eduarbo/flan36/docs/progress.md

# Progress

**Current mechanical revision: I. Overall keyboard: partial digital prototype.**

| Outcome | State | Evidence / next step |
|---|---|---|
| 36 Piantor key centers and angles | Checked | [Layout](../design/layout.json), upstream files and checker |
| Editable source and CAD exchange | Available | Native FCStd, parameters and [FreeCAD/StepUp examples](freecad.md) |
| KLP catalog and themed frames | RevI digital study | 38 source variants, 28 with qualified positions; six installed approved frame styles, per-key colors and configuration export/import |
| Wireless electronics and displays | Routed prototype | Both halves: DRC/ERC/parity 0, unconnected 0; exact connectors and hardware tests pending |
| Firmware and fabrication files | Digital candidate | Three compiled UF2 variants and source-bound Gerber/drill packages; supplied parts and physical acceptance pending |
| Printing and assembly | Pending | Fit coupon, sample caps and actual component measurements |
| Working keyboard | Pending | All keys, BLE, charging, sleep/wake and measured consumption |

## Revision I — October audit corrections

The current assembly adds the approved Hanafuda frame, repairs display/frame parameter dependencies and case USB access, and includes all 36 diodes and hot-swap sockets. Current delivery evidence and remaining prototype limits are recorded in the [audit correction report](reviews/2026-10-07-corrections.md).

Publication verified: **1,875 source files**, the online/offline viewer, print resources and thirteen rendered images match the tested source. The public viewer preserves the camera through case/frame changes and exports the selected configuration and exact STL kit. [Publication evidence](../validation/revI-audit-publication.json). This is a historical publication snapshot. Current routing and firmware evidence is in the [build continuation](reviews/2026-10-08-build-continuation.md); physical acceptance remains open.

The entries below retain their original historical snapshots.

## Revision I — readable right-hand artwork

Both halves now keep the same artwork direction. Game Boy's D-pad stays on the left and its buttons on the right; the right shell retains its existing corner radii and mounting geometry. The correction is recorded in the native document and carried through the material STL/STEP files, viewer and print kit. Historical documents retain their original interpretation. [Construction and checks](../design/frame-orientation.md).

## Revision I — approved viewer selection

The earlier withdrawal changed only the proposal gallery, leaving rejected shapes in the main viewer. The viewer now offers Talavera (default), Game Boy, SNES, Phone and iPod; Flan, Tape, Orbit, Manga, NES and Walkman are excluded from its selector, geometry and print kit. Saved and imported retired IDs migrate to Talavera with original colors and recoverable source JSON. Hanafuda remains approved but not integrated. [Correction and reproducible checks](../design/approved-viewer-selection.md).

## Revision I — approved gallery selection (earlier snapshot)

The user rejected Evangelion and requested its removal. The [current gallery](frame-proposals.md) now contains only Talavera, Game Boy, SNES, Phone, iPod and Hanafuda. The rejected proposal and its public previews were removed from the gallery. There is no pending artwork approval. Hanafuda integration remains pending; the main assembly and explorer are unchanged. [Selection record](../design/frame-selection.json).

## Revision I — historical R8 proposal

[R8](../design/proposals/frame-redesign-r8/) retained the six approved designs and proposed an Evangelion frame using M1's palette. That proposal was subsequently rejected and never installed. Historical source and verification receipts are preserved.

## Revision I — Hanafuda retained; historical R7 choices

The user selected Hanafuda with its R6 shapes and palette unchanged. Caramelo, Lucha, Cartucho 8 and Terminal were rejected; the previous Mecha was rejected for redesign. [R7](../design/proposals/frame-redesign-r7/) offered three Mecha and three Kumiko alternatives with exact dimensions, colors and matching review solids. Selection precedes artwork integration; the production assembly and main viewer are unchanged.

## Revision I — six new artwork directions, historical R6

R5 was rejected. [R6](../design/proposals/frame-redesign-r6/) proposed Caramelo, Lucha, Hanafuda, Mecha, Cartucho 8 and Terminal with exact paths, solid HEX colors, dimensioned sheets and matching editable FreeCAD review solids. Subsequent selection is recorded above; the frozen proposal files remain available.

## Revision I — corrected display seam and six exact proposals

The opening is now centered on the glass with 0.10 mm nominal clearance on all sides. It closes the exposed side bands without moving the display or raising the stack. The five approved bezels remain exactly 2.40 mm wide; their other artwork and colors are unchanged. [Correction and limits](../design/display-seam-implementation.md).

Flan, Tape, Orbit, Manga, NES and Walkman received [dimensioned R5 proposals](../design/proposals/frame-redesign-r5/), including editable review solids and actual mesh renders. This historical proposal was subsequently rejected and superseded by R6; its artwork was never installed. [Verified public source, viewer, print kit and R5 snapshot](../validation/revI-display-seam-public.json).

## Revision I — approved R4 frames (earlier snapshot)

Talavera, Game Boy, SNES, 2000s Phone and iPod now use the approved exact paths and solid palettes. The frame and Level shell rise 0.20 mm to Z13.59; the centered glass stays at Z13.39 and the pin row gains a 0.40 mm cover. Flan, Tape, Orbit, Manga, NES and Walkman retain their existing artwork pending redesign. Flan remains the default. [Construction and verification](frames-extra.md). Public source, viewer, images and an actual print-kit download match the implemented files. [Public readback](../validation/revI-approved-frames-public.json).

The entries below describe their historical snapshots. Their receipts retain original hashes.

## Revision I — frame fidelity correction

The first collection passed structural checks but did not preserve the selected compositions, and its support mask silently severed several decorations. The correction restores the reference motifs and adds per-feature rejection for unsupported artwork. [Reference comparison](frame-comparison.md) · [Digital checks](../validation/revI-frame-fidelity.json). Earlier verification receipts describe their original snapshots. Public source, images, viewer and downloaded print files match the corrected implementation. [Publication receipt](../validation/revI-frame-fidelity-public.json).

## Revision I — solid-color frame collection

Flan is the default frame in the native assembly, viewer and presets. Tape, Orbit, Manga, Talavera, Game Boy, NES, SNES, 2000s Phone, Walkman and iPod complete the new collection. Every design uses up to four solid colors in flush 0.4 mm co-print regions. The case, keys, electronics and 13.39 mm roof remain unchanged.

Older frame IDs migrate to Flan with the original saved bytes retained for recovery. Their colors, battery, cases and caps survive. The current exports contain only the eleven designs. [Collection and regeneration](frames-extra.md) · [Current digital checks](../validation/revI-frame-collection.json).

## Revision I — sculpted cap direction correction

The Normal and Saddle sculpted presets had the top and bottom rotations reversed. Both now place the higher edges away from the home row. This changes 20 rotations per preset, with no changes to stems, seating or key centers. Actual side-profile previews replace the former side-by-side arrangement. **Caps → Fix top/bottom slopes** repairs older configurations without replacing custom variants, colors or other components. [Directional checks](../validation/revI-cap-rows.json).

## Revision I — floor battery and Level case

The glass, frame and new **Level** upper shell share a **13.39 mm** plane: **1.41 mm lower** than the previous frame. Both batteries sit directly on the 1.4 mm case floor. The nice!nano PCB is at 8.2 mm and the nice!view PCB at 11.49 mm. Key centers and the selected caps' 17.87 mm height are unchanged.

Level covers switch bodies using the existing removable plate and its three screws. Its openings reserve the full 3.5 mm cap travel. The current collection has eleven flush frames, both battery profiles and twenty-seven linked color themes. [Dimensions and connector qualification](level-stack.md) · [Current digital delivery checks](../validation/revI-level-delivery.json).

The Samtec display pair is dimensioned as a nominal candidate. Finished nice!view hole fit, actual engagement, printed strength and physical assembly remain unqualified. The boards remain unrouted.

The entries below describe their historical snapshots. Current files may supersede their geometry; original receipts retain the hashes of the files tested at the time.

## Earlier revision I — slimmer stack and flush decoration

The electronics cover now targets **14.8 mm** from the case underside, with a **12.4 mm display PCB datum**. The battery moves 0.8 mm toward USB without rotation. A lateral PH connector, retained display socket and recessed underside reset make the interfaces explicit. Both Adafruit 1570 and 301230 have their own continuous nominal lead routes.

Handheld, Retro TV, Cyberpunk, Cartridge, Arcade, Mecha and Kintsugi use **0.4 mm flush color volumes** with at least 0.8 mm nominal backing. The ten frame styles, 36 original key transforms, case contour and magnetic interface are preserved. Selected KLP caps still set the overall 17.87 mm height, excluding feet.

[Design and service sequence](slim-flush.md) · [Historical digital delivery checks](../validation/revI-slim-flush.json). Exact supplied parts, wire flex, printed fits and electrical operation remain unqualified.

## Earlier revision I — keycap palettes and creative frames

Color all keys, a row, a column or one key, on either half or both. Eight keycap palettes and sixteen coordinated global themes provide starting points. Personal palettes can be saved, imported and exported; configurations retain all 36 colors without changing key shapes or rotations. [Color editor](customize.md#keycap-colors).

Cartridge, Arcade, Mecha and Kintsugi bring the frame catalog to ten. Their relief is actual printable geometry; previews and print kits use the corresponding meshes. Native FreeCAD preserves custom colors through save/reopen. [Frame guide](frames-extra.md).

The [measured support study](slim-mount-study.md) covers both halves, both batteries and all ten frames. Integrating plate washers removes six loose parts; optional integrated battery saddles remove two more. Neither changes height. A 15.6 mm plain roof clears modeled static geometry, but overall height stays **17.87 mm** with the selected caps, excluding feet. A 14.8 mm roof intersects the JST envelope. Display/sled extraction crosses modeled battery leads in all three recipes; cable routing, connector engagement and physical fit remain open. Separately named experimental STEP/STL files are included; the reference print kit keeps its original stack.

Publication verified: all **1,013 implementation files** match the anonymous archive. The public viewer passes desktop/touch checks, per-key palettes, coordinated themes, configuration/GLB round trips and six selected print kits. [Public readback](../validation/revI-customization-publication.json). Physical keyboard acceptance remains open.

## Earlier revision I — shared frame corner and height study

The USB-side frame corner now uses the case's actual R2.4 arc. The previous R1.2 frame produced a roughly 0.497 mm diagonal overhang. The cavity, plate clearance and beveled profiles follow that shared definition. Case/PCB outlines and key positions are unchanged. [Close view and height comparison](design.md#can-the-stack-be-thinner) · [Native corner check](../validation/revI-frame-corner.json).

That snapshot’s 16.6 mm plain / 17.2 mm decorated cover was **not a proven minimum**. A preliminary left-half study lowers the display and evaluates 15.6 / 16.2 mm covers; actual connector engagement and tolerances remain open. A 14.8 mm plain cover intersects the existing battery-connector envelope. Printable source heights remain unchanged. [Study](../validation/revI-stack-study.json) · [Correction scope](../design/corner-stack-workflow.json) · [Independent review](../validation/revI-corner-stack-review.json).

Publication verified: all **922 implementation files** matched the anonymous archive; public Pages, the corner image, desktop/touch UI and selected print exports matched the tested source. [Public readback](../validation/revI-corner-stack-publication.json).

## Revision I — linked colors, print kits and component models

Sixteen color themes coordinate the frame with the case rim. Per-half body, plate and three detail colors survive JSON and local browser storage; applying a theme preserves the selected shapes and keycaps. Print kits include the selected native STL parts, generic color 3MF files, supports, washers and the actual screw/magnet instructions. No clip variant is claimed. [Themes and printing](themes-printing.md).

The nice!nano v2 and nice!view now have nominal board/contact/package geometry. Choc v1 uses licensed KiSwitch meshes; the power and reset switches use KiCad models placed at the existing footprints. The narrower nano board uses scalloped support ledges, leaving the underside pad reserves clear. [Component evidence and limitations](../components/README.md).

The offline explorer passed desktop/touch emulation down to 320 px, per-half configuration and custom-color GLB export. Native FreeCAD preserved colors through save/reopen. Selected print kits preserve native STL bytes and closed, oriented 3MF surfaces. [Configuration checks](../validation/revI-theme-customization.json) · [Print checks](../validation/revI-print-kit.json).

With 4× CPU throttling, orbit p95 is **16.7 ms**, frame choice **68 ms** and case choice **124 ms**, with no orbit long tasks. First readiness takes **8.7 s** in this local stress test; the self-contained viewer is about **45 MiB**. Physical-phone loading and timing remain unmeasured. [Measurement](../validation/revI-theme-performance.json).

Publication verified: all **914 implementation files** matched the anonymous source archive. The actual public viewer passed desktop/touch emulation, 16 theme previews, linked colors, JSON/GLB and selected print-kit checks. All 11 relative KiCad STEP models passed geometry, footprint-placement and colored-surface readback. [Public verification](../validation/revI-themes-components-publication.json).

**Still partial:** Bambu Studio needs manual palette mapping; GUI import/save/reopen has not been validated. Hotswap socket registration, actual connector contacts, the 7 versus 8.8 mm display connection and physical fit remain open. [Scope and review](../design/themes-components-workflow.json).

## Revision I — local curves and interchangeable cases

The contour now follows each thumb’s angle with local tangent rounds, plus softer finger corners. Solid, Color rim and Terrace are real base/plate variants. Per-half choices and optional exposed display stacks transfer between the explorer, JSON, GLB and native FreeCAD. [Case gallery and files](cases.md) · [Decision record](../validation/revI-case-variants-review.json).

Native solids, all six case pairs, mixed configuration save/reopen and exact selected GLB meshes passed. The explorer uses distinct mesh previews in a two-column grid; desktop and touch emulation pass through 320 px. Local 4× CPU checks: orbit p95 **16.8 ms**, case selection p95 **123.5 ms**, frame selection p95 **68.6 ms**, zero orbit long tasks. Publication verified: **824 source files** match the anonymous archive; public viewer, case gallery images, desktop/touch interactions, per-half case selection, open covers and exact JSON/GLB exports pass. [Public readback](../validation/revI-case-variants-publication.json). Physical-phone timing and printed fit remain untested.

## Previous revision I — uniform exposed rim

That revision made the case, switch plate and PCB follow a **curved lower thumb edge and LCD-aligned flank**. The 2.55 mm thumb-side protrusion is removed without moving keys or widening the bay. Finger margins stay 4.75 mm; the pinky foot retains 90° backbone corners with R0.8 blends. View tools remain below the model, with clearer Part links/Fit view feedback and full-row explorer hover. [Measured view](images/revI-rim.png) · [Correction review](revI-review.md#key-aligned-local-curves-and-case-variants).

Publication verified: **785 source files** match the anonymous download. The public viewer passes desktop/touch emulation, layers, frame/battery selection, JSON and exact GLB checks; the dimensioned image matches its source. [Public readback](../validation/revI-rim-publication.json).

That revision’s local viewer check: 4× CPU orbit p95 **16.7 ms**, theme change p95 **64.6 ms**, and zero orbit long tasks. Desktop/touch emulation, layers, JSON and exact GLB exports pass. Physical-phone timing remains unmeasured.

## Earlier revision I — Contour, magnetic frames and dual battery cradle

The case and PCB follow the stepped reference: rectangular pinky foot, shallow recess and continuous thumb fan. The **117 × 92.85 mm** case uses 20 control corners at R0.8. All 36 original key transforms remain fixed.

Three captive magnet/steel stations release each frame vertically; five independent internal M2 screws retain the structure without adding perimeter lobes. Both nominal **Adafruit 1570 and 301230** envelopes share one low saddle, aperture and captured cage. The viewer and FreeCAD configuration include battery selection.

The viewer passed offline desktop and emulated mobile checks, exact selected battery/frame GLB exports and JSON round trips. Local 4× CPU measurements: **16.8 ms orbit p95**, **67 ms frame-change p95**, zero orbit long tasks. Physical-phone performance remains untested.

The earlier slot/copper conflict and displaced mount were corrected without relaxing the 0.5 mm edge rule. Native solids, six frame styles, two battery envelopes, saved configurations, CAD-derived renders and the viewer are checked as digital artifacts. Routing, connector qualification, printed retention, charging and BLE remain open.

Publication verified: all **775 source files** matched the anonymous archive; public viewer bytes and actual browser-loaded geometry matched the tested source. Desktop/touch emulation, batteries, frames, JSON and exact selected GLB geometry passed. [Public readback](../validation/revI-publication.json).

[Review and limits](revI-review.md) · [Mechanical checks](../validation/revI-mechanical.json) · [PCB readback](../validation/revI-electrical.json) · [Service/coupons](../validation/revI-service.json).

## Multicolor frame previews

Handheld, Retro TV and Cyberpunk now use distinct body, detail and accent colors on the existing raised faces. Larger upright previews show the corresponding meshes and palettes; one click applies both. Body-color overrides remain independent per half and survive JSON export/import. The shared palette also drives the GLB materials, FreeCAD configuration import and frame comparison image.

The former thumbnails referenced different STL files, but used one green material and a distant oblique view. Their distinct-image test did not establish readable design details. Current checks identify actual left/right raised features, preserve every original vertex/normal/triangle and verify the exported material colors. Geometry and manufacturing status remain unchanged.

Verified on the public viewer, including mobile emulation, JSON and GLB; all 579 published source files matched the tested commit. FreeCAD applied four colors per native theme/half and preserved them through save/reopen. The 4× CPU benchmark retained a 16.7 ms orbit p95 and 57.5 ms theme-change p95.

[Color and print guide](customize.md#print-a-themed-display-frame) · [Checks](../validation/viewer-multicolor.json) · [Public readback](../validation/viewer-multicolor-publication.json) · [Correction scope](../design/viewer-multicolor-workflow.json).

## Persistent component sidebar

All 12 component entries remain visible while their details scroll or collapse. Hover, focus or select a part to highlight it; the connecting line ends at its own sidebar entry. Frame previews still apply in one click. Desktop, 390 px and 320 px touch layouts, short landscape, configuration and exact GLB export passed local and public checks.

The previous floating-tag iteration passed functional tests but missed the intended sidebar relationship and had no latency acceptance. Its anchor search could run up to 192 full-scene intersection queries per camera update. Surface searching now pauses during gestures and resolves only the active component afterward; rendering is coalesced and highlights are reused.

On the same Chromium 152 setup at 1200 × 800 with 4× CPU throttling, **p95 orbit frame interval fell from 1,616.5 to 16.8 ms**, with 59 long tasks reduced to zero. **Frame-change p95 fell from 1,692.4 to 59.0 ms**. These are local benchmark results; physical-phone performance remains untested.

[Usage guide](viewer.md) · [Checks and measurements](../validation/viewer-sidebar.json) · [Public readback](../validation/viewer-sidebar-publication.json), including all 571 source-commit files · [Correction scope](../design/viewer-sidebar-workflow.json). Historical acceptance of the first visual explorer remains in its [original receipt](../validation/viewer-ux-publication.json).

## Revision H — continuous edge and printable themes

The user’s red-line reference replaces the old display notch and thumb wing with one straight inner case flank. The case is approximately **8.1 mm narrower**, keeping every switch center and angle. Sixteen intentional corners use a common **1.2 mm radius**.

Handheld, Retro TV and Cyberpunk add actual roof relief within the same bay. Plain styles remain available. The high cover ends before the thumb; base and plate continue the aligned edge. Both KiCad contours match the new CAD reference without moving footprints or changing nets. There are still **26 DRC violations and 104 unconnected items per half**.

Publication verified: all **561 source files** matched the anonymous archive. Public HTML and the browser-loaded scene matched the tested source; layers, orbit, all three themes, JSON, selected GLB geometry and narrow-screen emulation passed. Actual phone and hardware tests remain pending. [Publication receipt](../validation/revH-publication.json).

[Revision review](revH-review.md) · [Keycap checks](../validation/revH-keycaps.json) · [Mechanical checks](../validation/revH-mechanical.json).

## Revision G — keycaps and frames

Opaque covers replace revF’s side rails. The separate display sled stays in place. Smooth, beveled and faceted styles share the same mounting centers, inner cavity and service openings. Bay width and top height remain 24 and 16.6 mm.

The viewer selects KLP variants by position/orientation, checks complete combinations and writes a JSON configuration used by the FreeCAD macro. GLB exports carry the active configuration. The cap check is separate from solid-part collision checks, which did not include KLP meshes in revF.

Documentation, current CAD labels, viewer and new render captions are in English. The [parts guide](parts.md) separates references from alternatives and adds technical links, supplier photos and Typeractive pack quantities. Conflicting part numbers and missing exact datasheets are kept visible.

Publication verified: an anonymous archive matched all **404 files** of the design commit; public viewer bytes matched the tested source. Keycap/frame selection, JSON round trip, exact selected GLB vertices, layers, rotation and narrow-screen behavior passed on the public URL. [Publication receipt](../validation/revG-publication.json).

[Review and limits](revG-review.md) · [Keycap checks](../validation/revG-keycaps.json) · [Mechanical checks](../validation/revG-mechanical.json).

## Earlier revisions

- **RevD:** wide side-by-side electronics and one display; visual direction discarded. The render survives only in Git history.
- **RevE:** 24 mm stacked bay, two displays and a 19 mm cover. CAD-derived images replaced the stale revD render.
- **RevF:** recessed battery opening, moved controller/display and 16.6 mm open rails. Native FreeCAD source added. Approximate case depth became 94.5 mm; width remained 126.2 mm because the thumb layout stayed unchanged.

RevF’s CAD/StepUp exchange, anonymous source download and public viewer were checked; physical acceptance was not. [Historical review](revF-review.md) · [publication receipt](../validation/revF-publication.json).

On September 22, 2026, Eduardo selected **Flan36** and the **Outline** logo. The current presentation shows only that selection. On September 23, the rename was extended to the repository, Pages site, current native filenames and new configuration exports. Legacy configuration imports remain supported. Geometry and unfinished electrical/physical requirements are unchanged.

The LCD-flank/curved-thumb and viewer correction is published. Anonymous source readback verified all **788 implementation files**; public browser checks passed for individual visibility, Solo/Show all, temporary X-ray hover, fixed View controls and mobile layouts. [Publication receipt](../validation/revI-lcd-curve-publication.json). Physical assembly and electronics acceptance remain open.
