eduarbo/flan36/docs/frame-proposals/index.html

← 3D explorer

Six selected designs

# Your frame collection.

Talavera, Game Boy, SNES, Phone, iPod and Hanafuda. The approved artwork and palettes stay exactly as selected.

Talavera, exact frame artwork

In the current assembly

## Talavera

#F1E6CA#244E91#C36443#244E91

Game Boy, exact frame artwork

In the current assembly

## Game Boy

#DCD6BA#42454D#973C60#A6A392

SNES, exact frame artwork

In the current assembly

## SNES

#D1D0C9#464751#746198#ACA0C2

2000s Phone, exact frame artwork

In the current assembly

## 2000s Phone

#263C55#B8BBB5#87AD67#455469

iPod, exact frame artwork

In the current assembly

## iPod

#F0EEE5#656F79#AFB4B1#D8D9D2

Hanafuda, exact frame artwork

In the current assembly

## Hanafuda

#F1E7D2#252B2E#D84932#456348

## Exact artwork, editable geometry.

The previews use the approved millimetre paths and HEX colors. The frame face stays at Z13.59 mm, with a uniform 2.40 mm screen bezel and the current 13.90 × 30.50 mm opening.

Printing and integration

The design targets a 0.4 mm nozzle and 0.2 mm layers. Features, bonding and physical fit still need slicing and a sample print. No decoration rises above the frame face. The LCD content in the previews is illustrative.

All six designs are integrated into the native assembly, main explorer and registered print kit. The frozen proposal files remain the approval reference.
