eduarbo/flan36/design/proposals/display-seam-r1/comparison.png

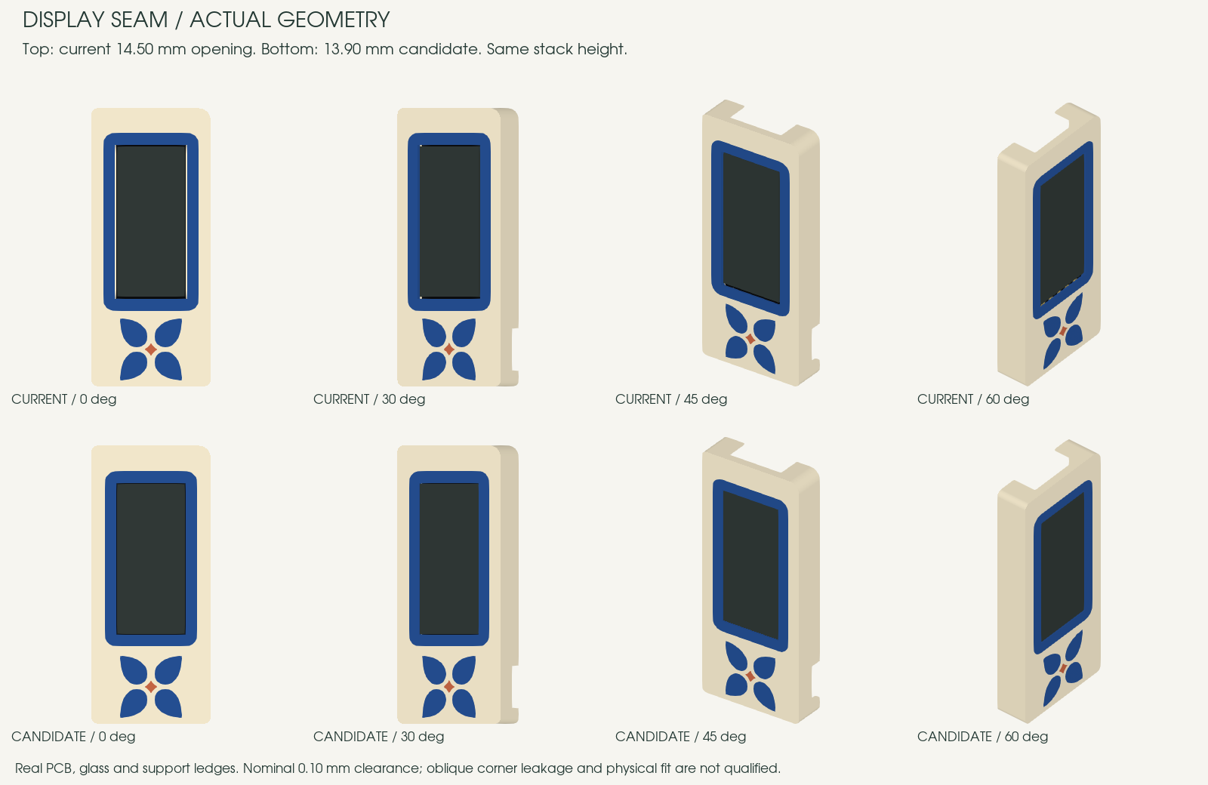
design/proposals/display-seam-r1/comparison.png
