eduarbo/flan36/design/proposals/frame-master-r4/flan-dimensioned.png

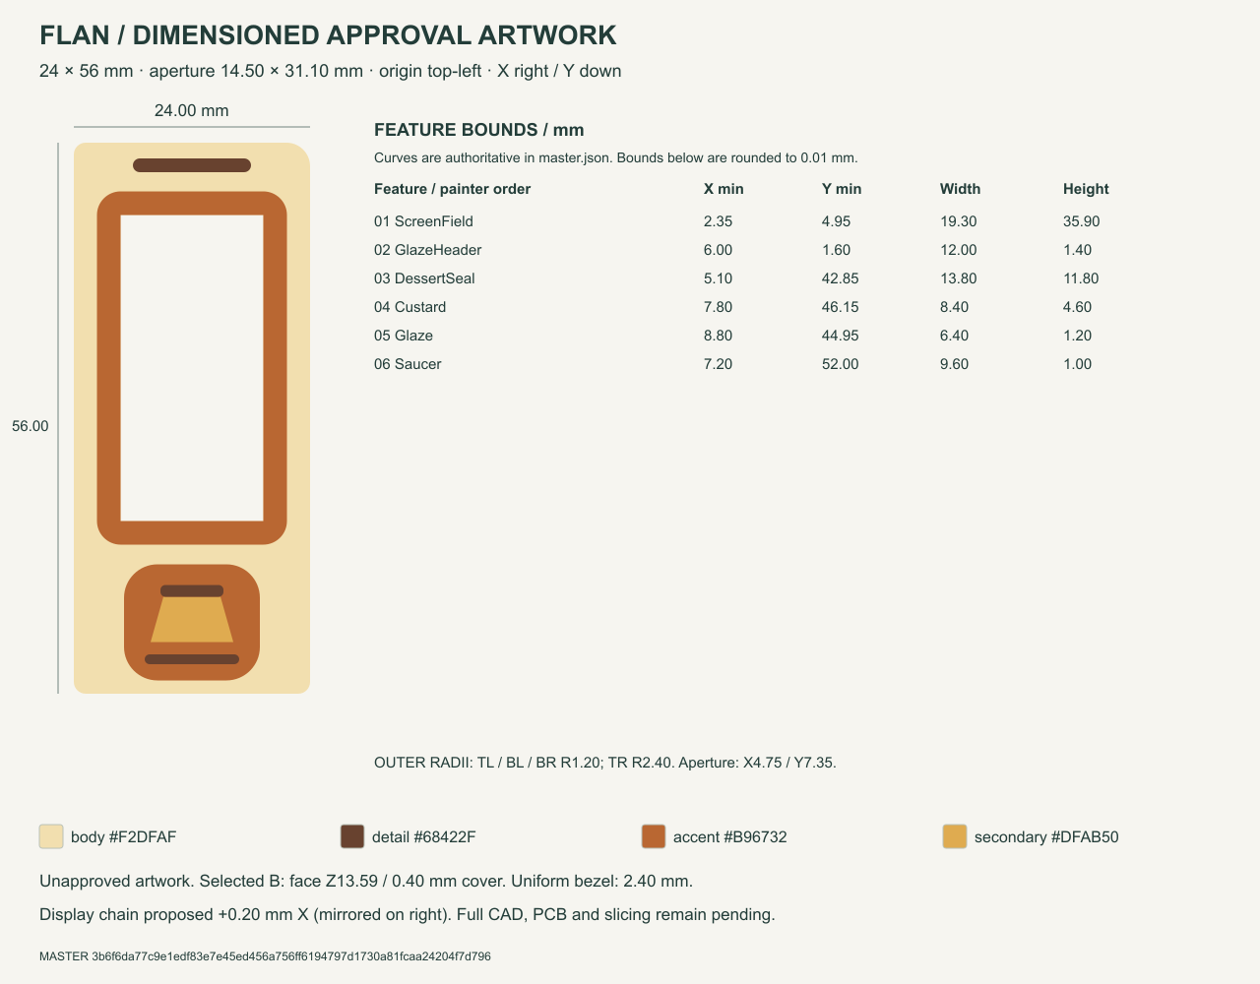
design/proposals/frame-master-r4/flan-dimensioned.png
