eduarbo/flan36/design/proposals/frame-master-r4/gameboy-dimensioned.png

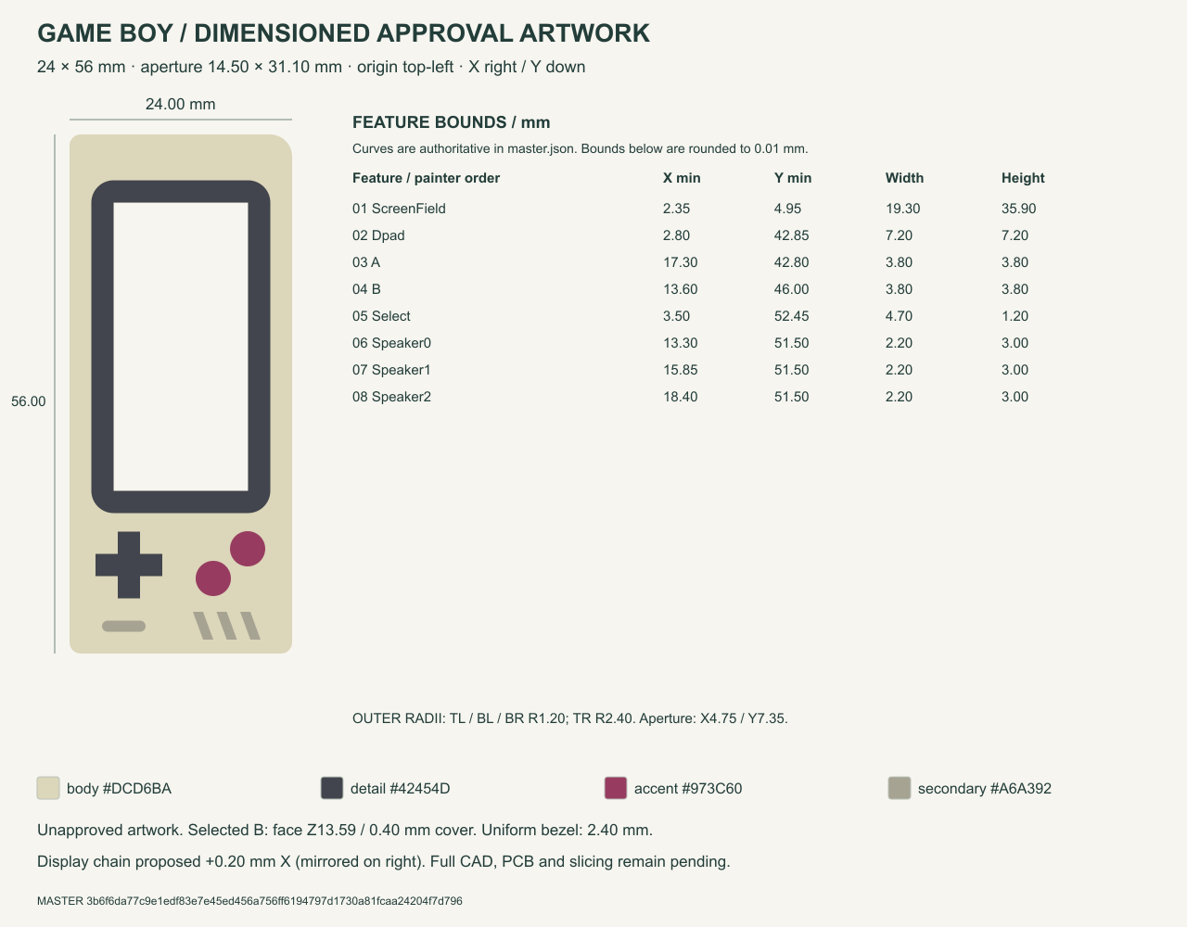
design/proposals/frame-master-r4/gameboy-dimensioned.png
