eduarbo/flan36/design/proposals/frame-master-r4/phone-dimensioned.png

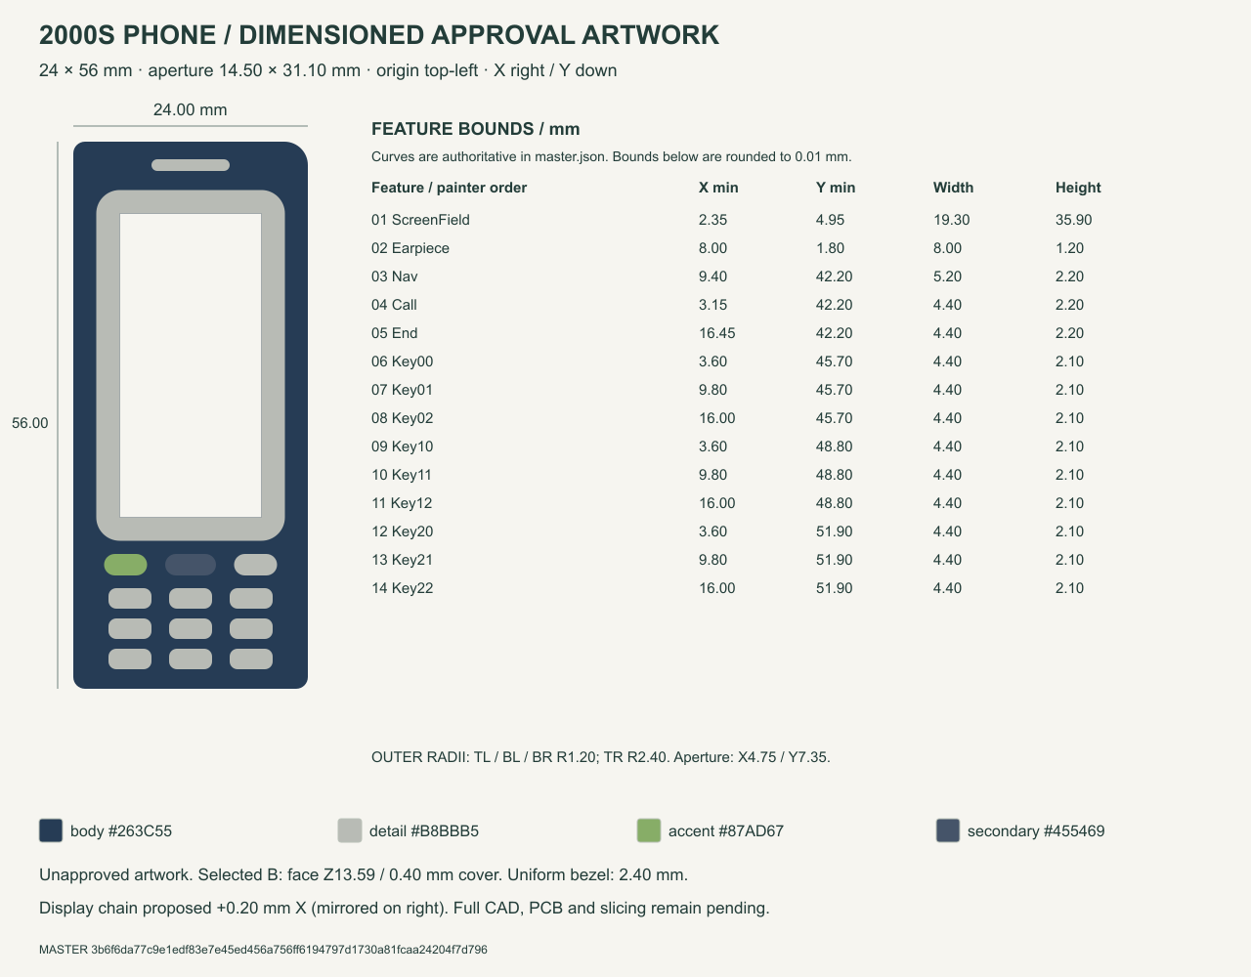
design/proposals/frame-master-r4/phone-dimensioned.png
