eduarbo/flan36/design/proposals/frame-master-r4/walkman-dimensioned.png

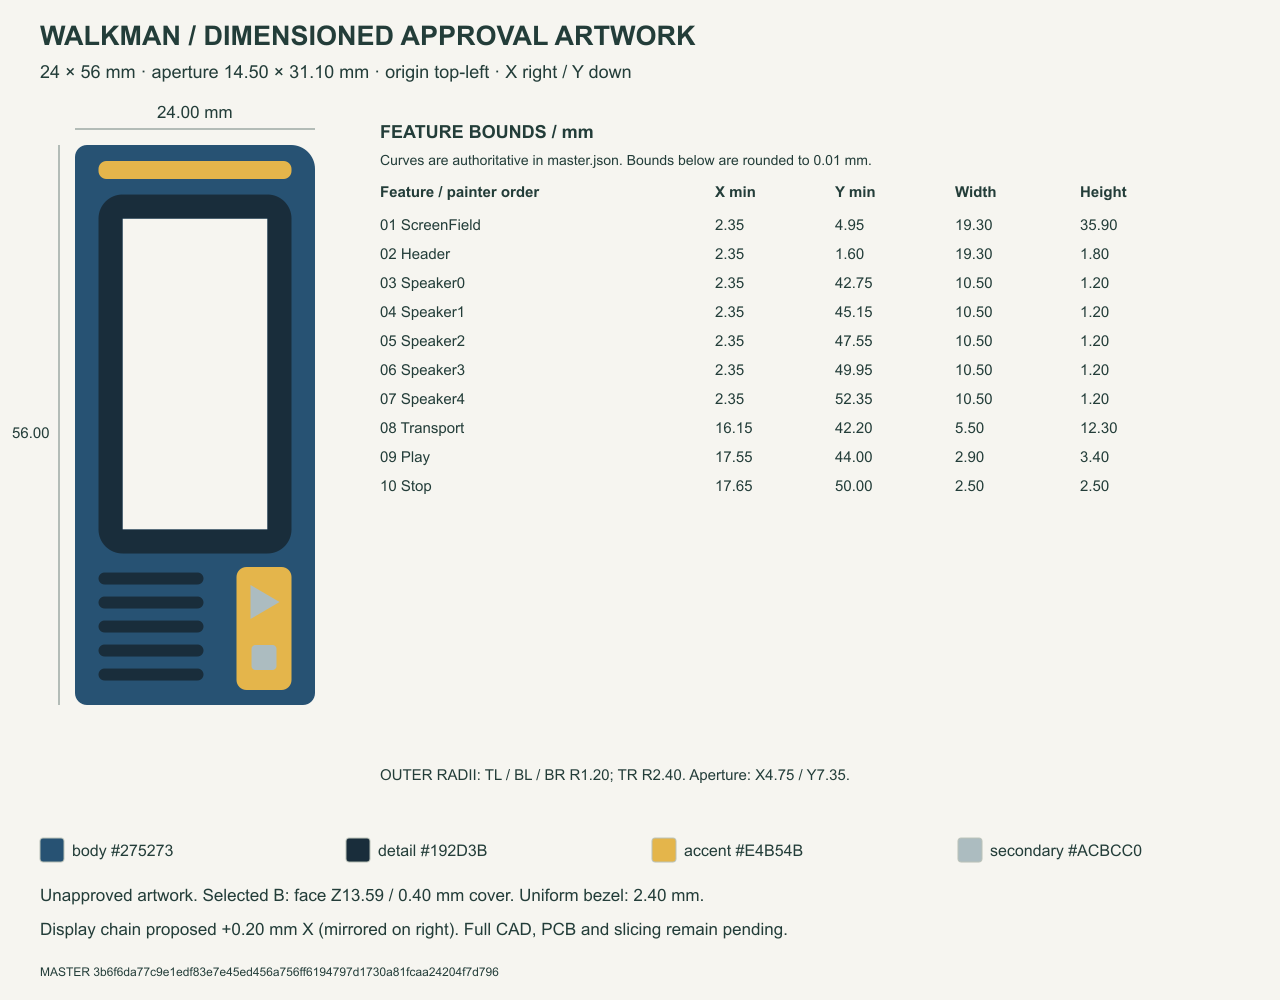
design/proposals/frame-master-r4/walkman-dimensioned.png
