eduarbo/flan36/design/proposals/frame-redesign-r6/collection-a.png

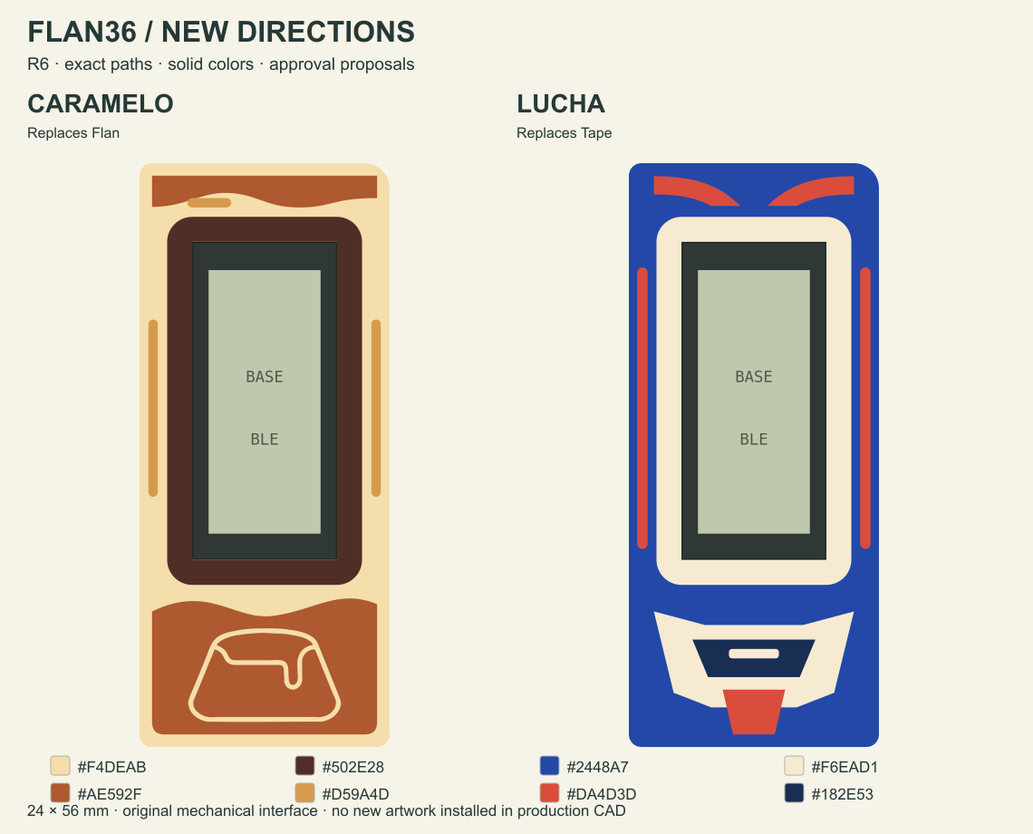
design/proposals/frame-redesign-r6/collection-a.png
