eduarbo/flan36/design/proposals/frame-redesign-r6/collection-b.png

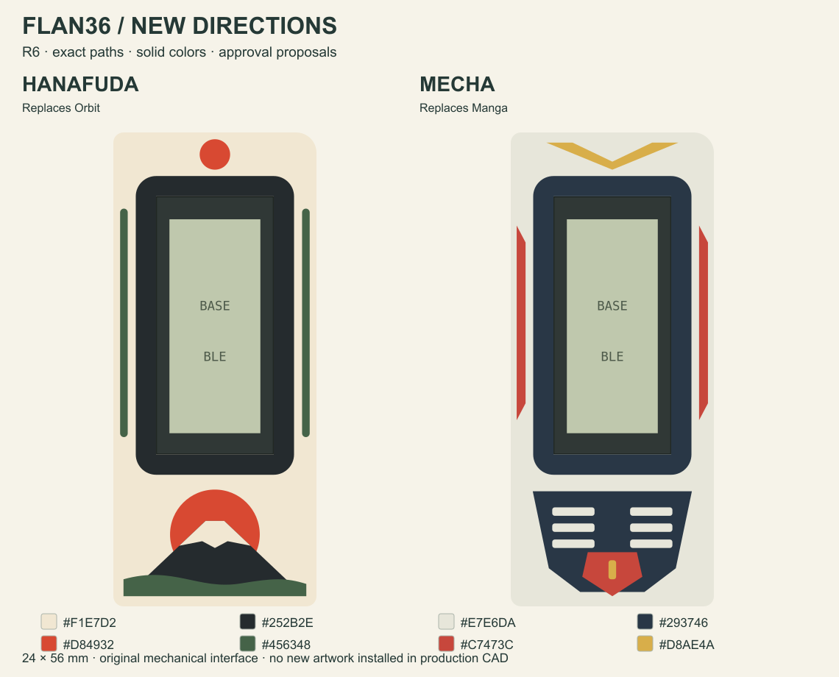
design/proposals/frame-redesign-r6/collection-b.png
