eduarbo/flan36/design/proposals/frame-redesign-r6/collection-c.png

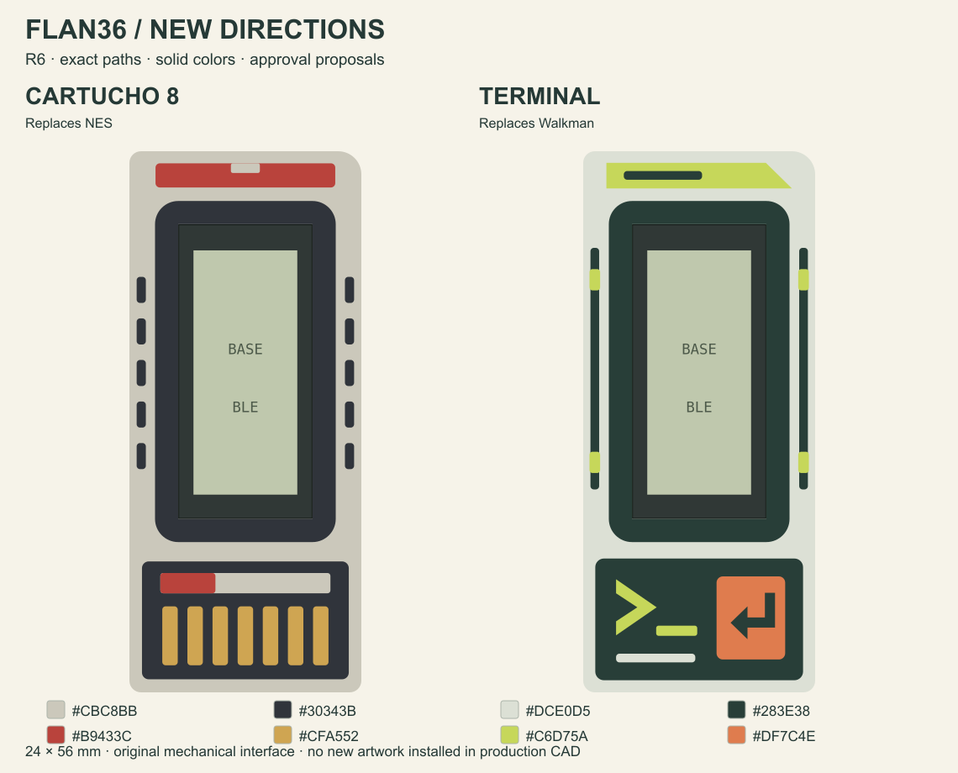
design/proposals/frame-redesign-r6/collection-c.png
