eduarbo/flan36/design/proposals/frame-redesign-r6/collection.png

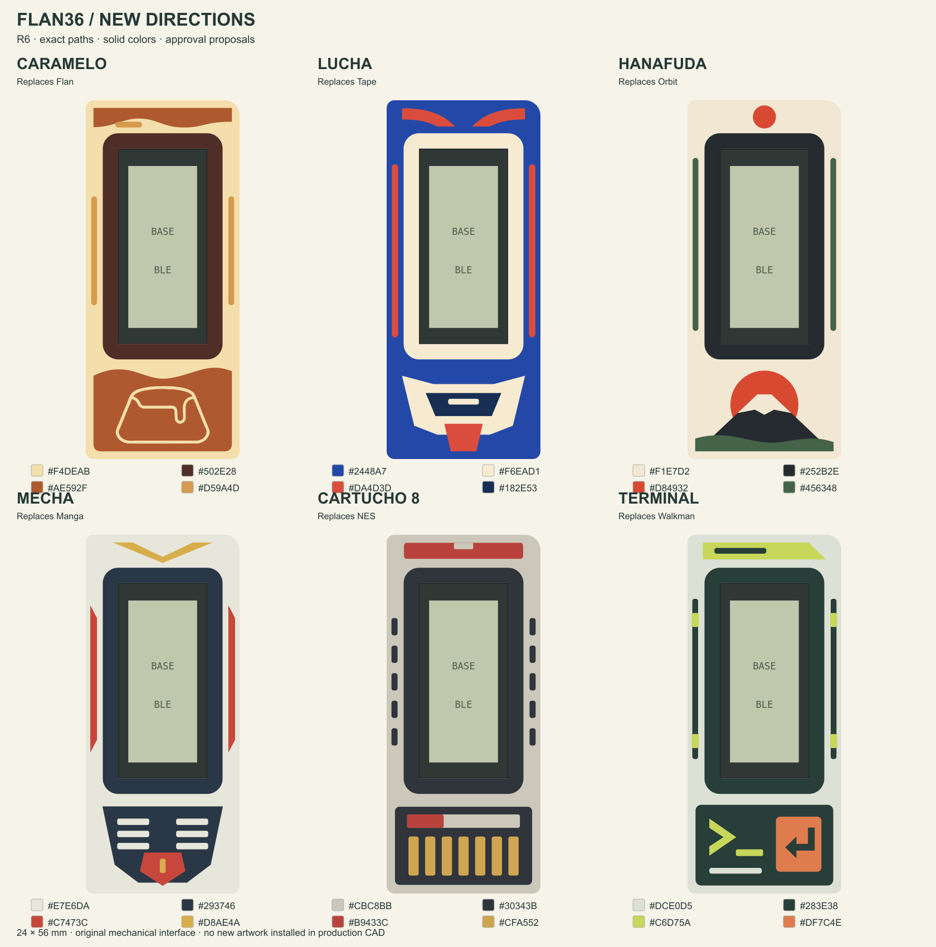
design/proposals/frame-redesign-r6/collection.png
