eduarbo/flan36/design/proposals/frame-redesign-r6/flan-card.png

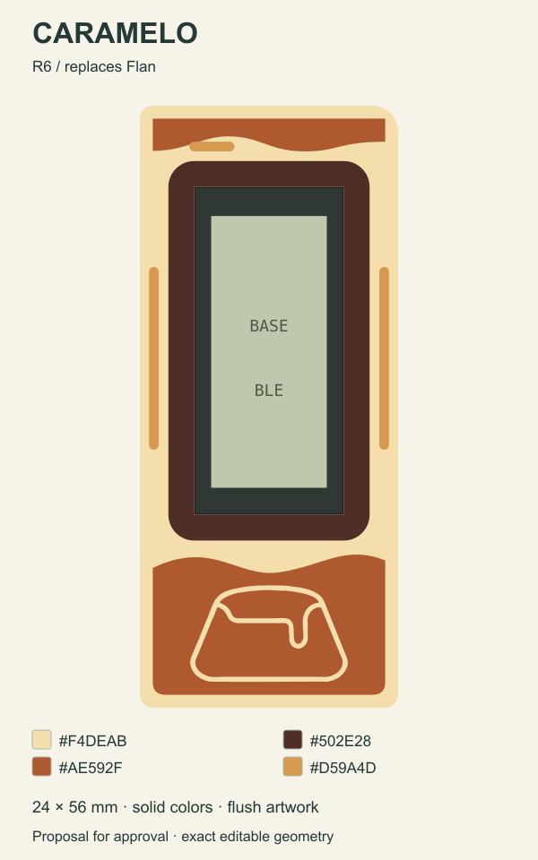
design/proposals/frame-redesign-r6/flan-card.png
