eduarbo/flan36/design/proposals/frame-redesign-r6/flan-dimensioned.png

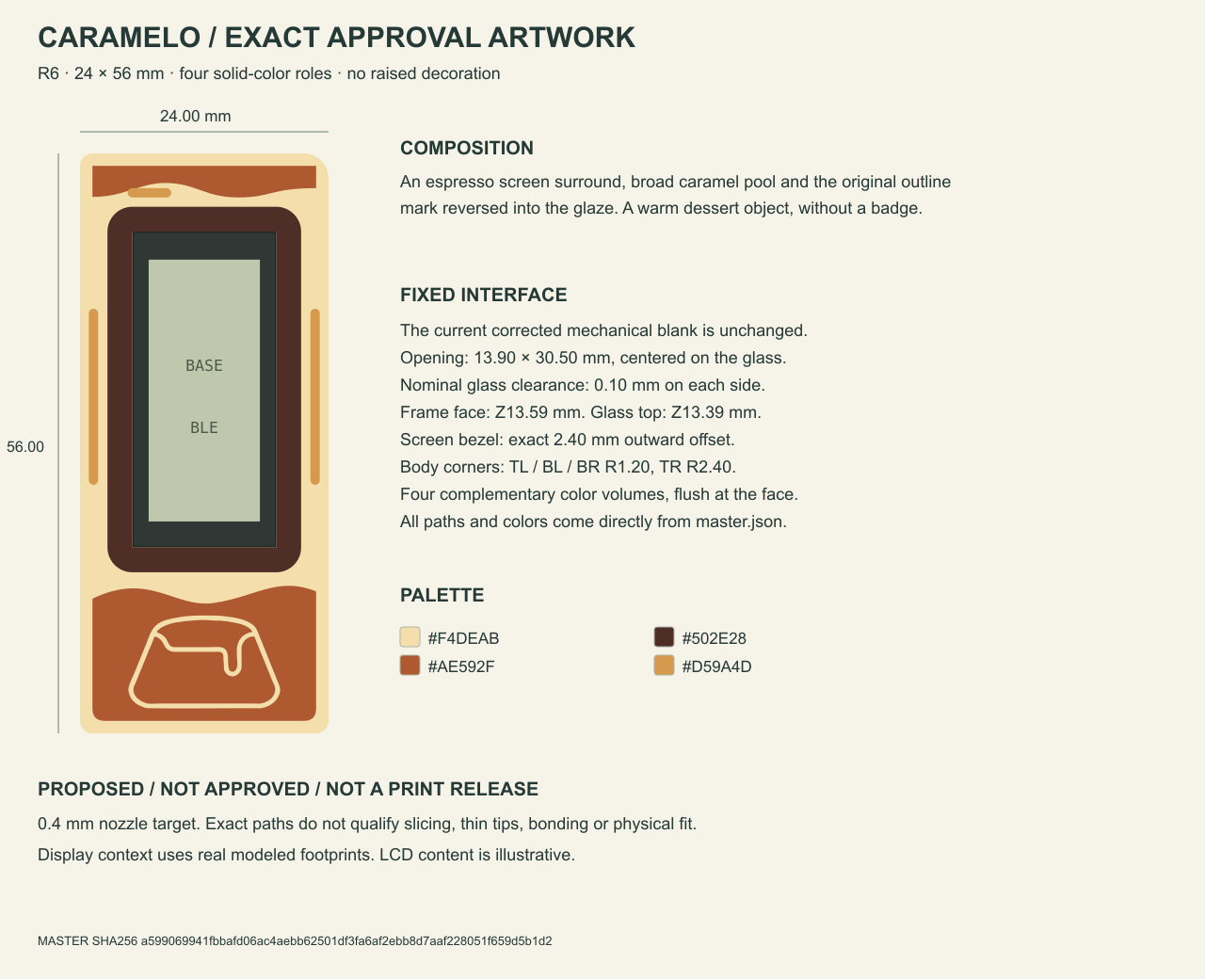
design/proposals/frame-redesign-r6/flan-dimensioned.png
