eduarbo/flan36/design/proposals/frame-redesign-r6/manga-card.png

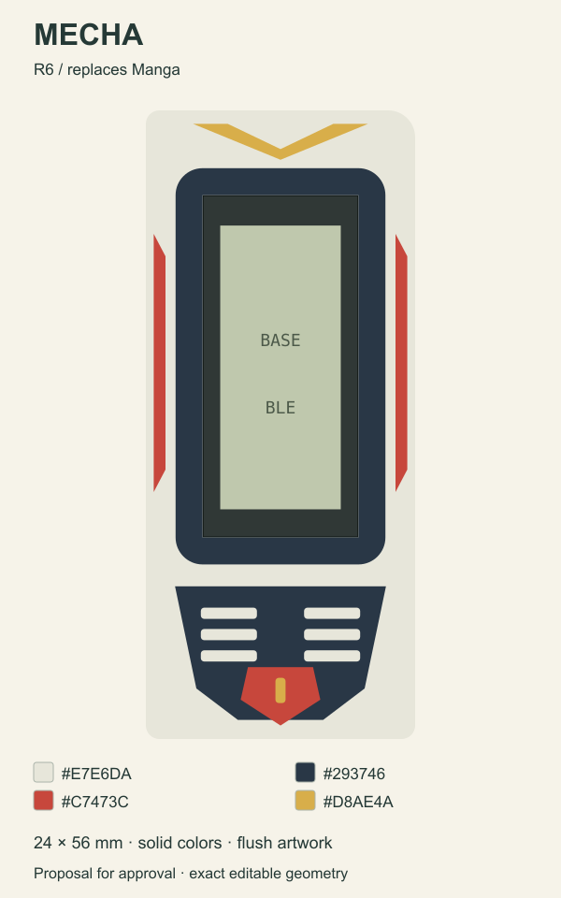
design/proposals/frame-redesign-r6/manga-card.png
