eduarbo/flan36/design/proposals/frame-redesign-r6/manga-dimensioned.png

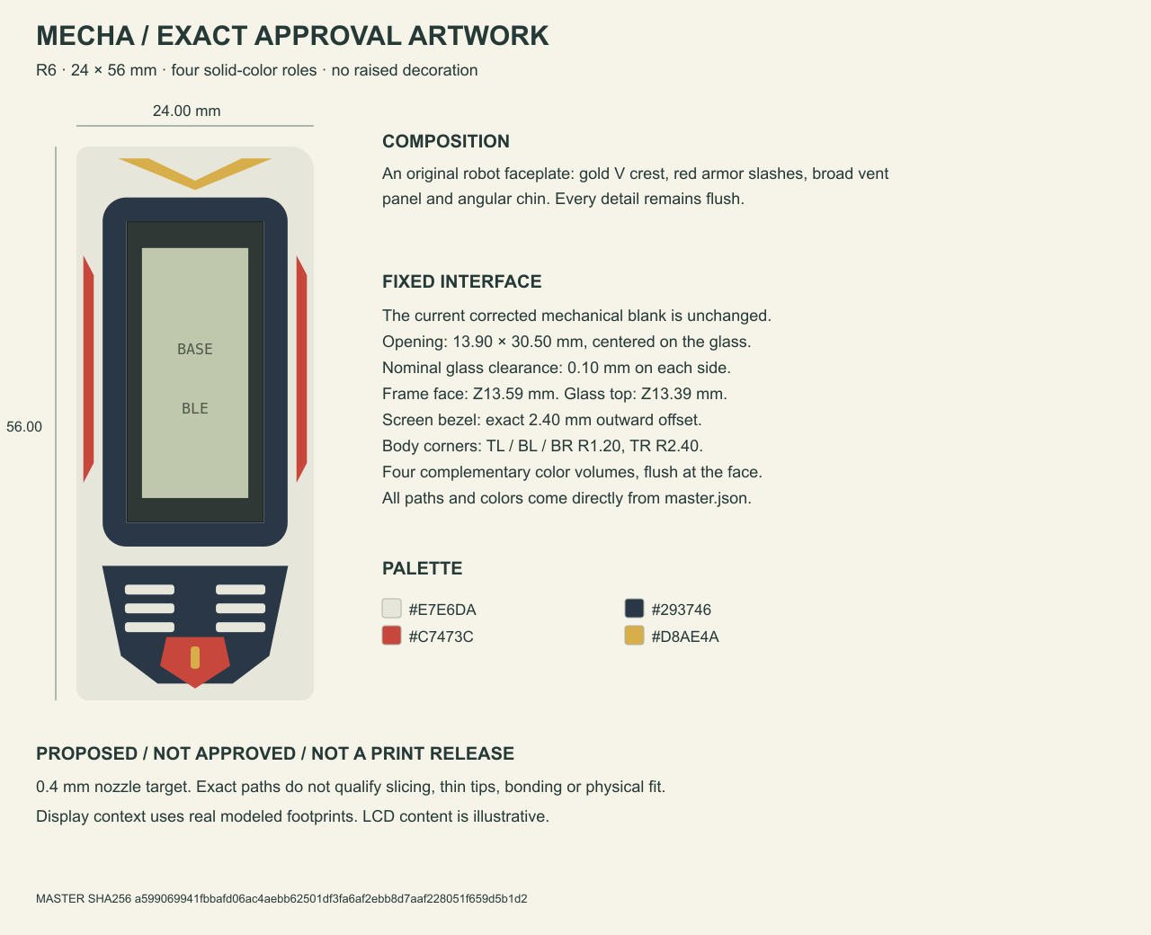
design/proposals/frame-redesign-r6/manga-dimensioned.png
