eduarbo/flan36/design/proposals/frame-redesign-r6/native-review.png

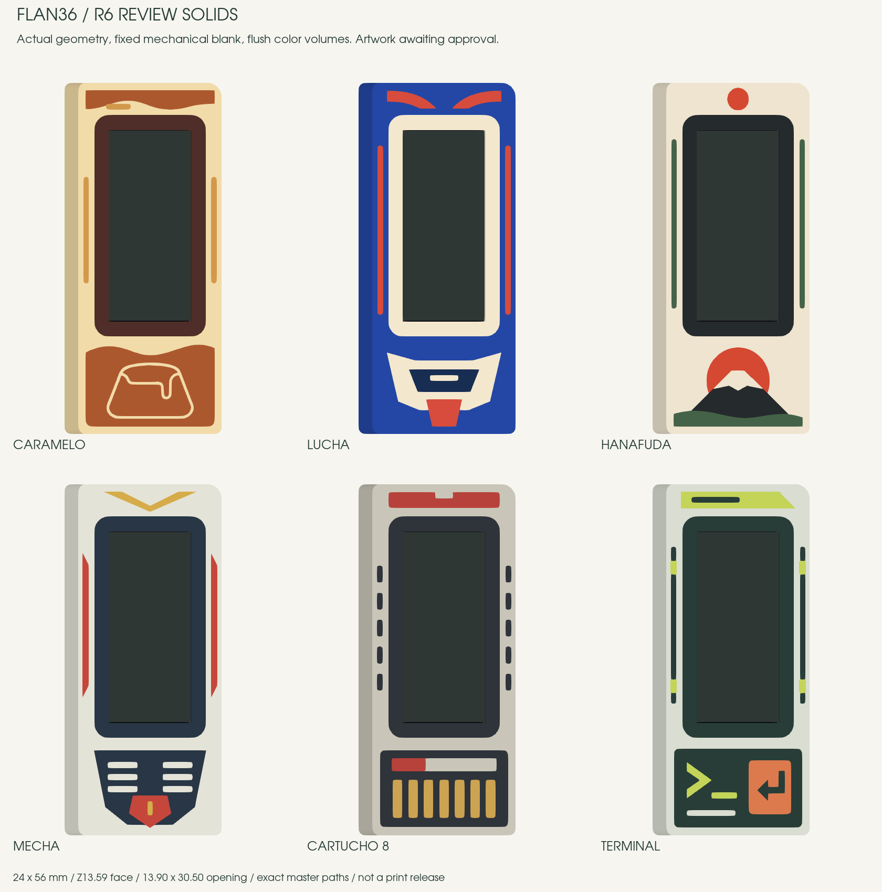
design/proposals/frame-redesign-r6/native-review.png
