eduarbo/flan36/design/proposals/frame-redesign-r6/tape-card.png

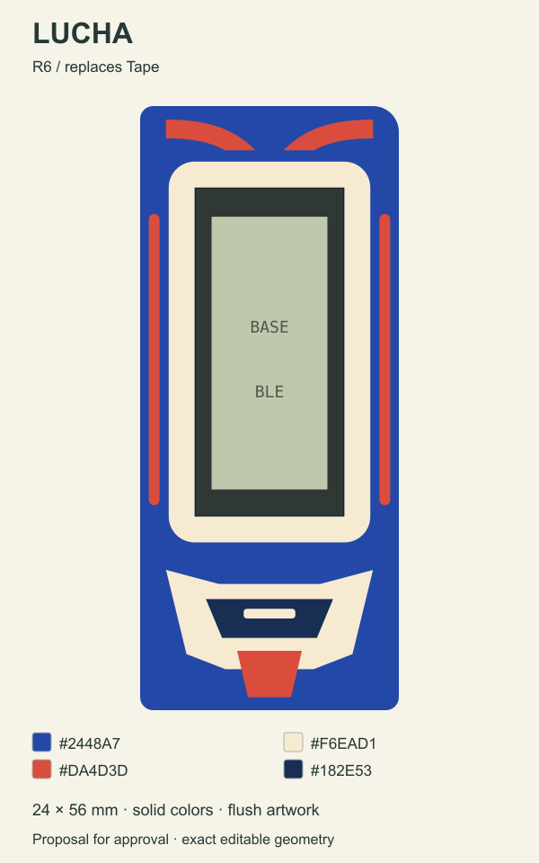
design/proposals/frame-redesign-r6/tape-card.png
