eduarbo/flan36/design/proposals/frame-redesign-r6/walkman-dimensioned.png

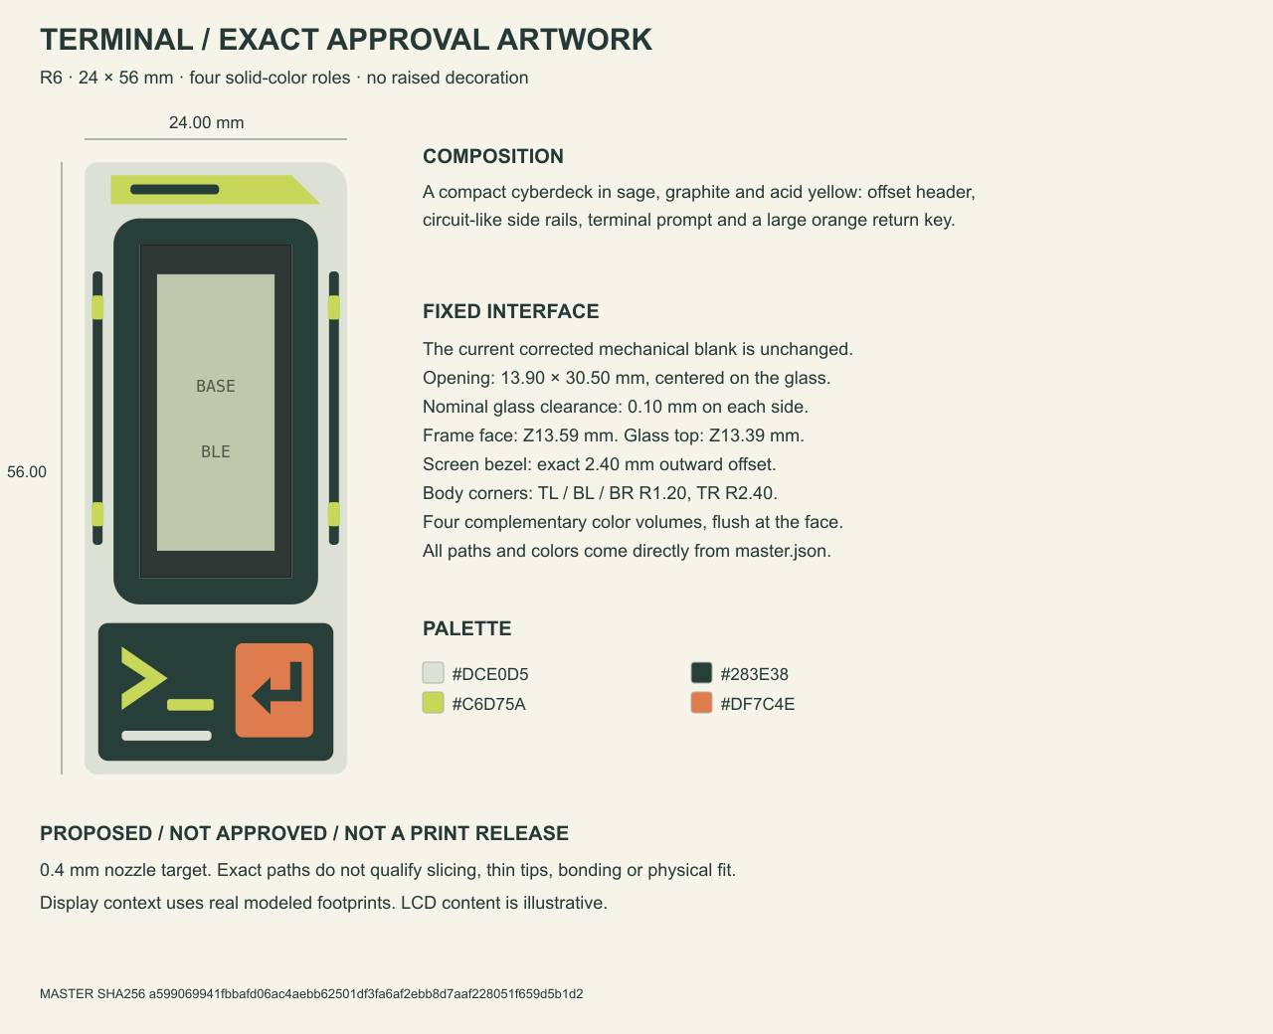
design/proposals/frame-redesign-r6/walkman-dimensioned.png
