eduarbo/flan36/design/proposals/frame-redesign-r7/collection.png

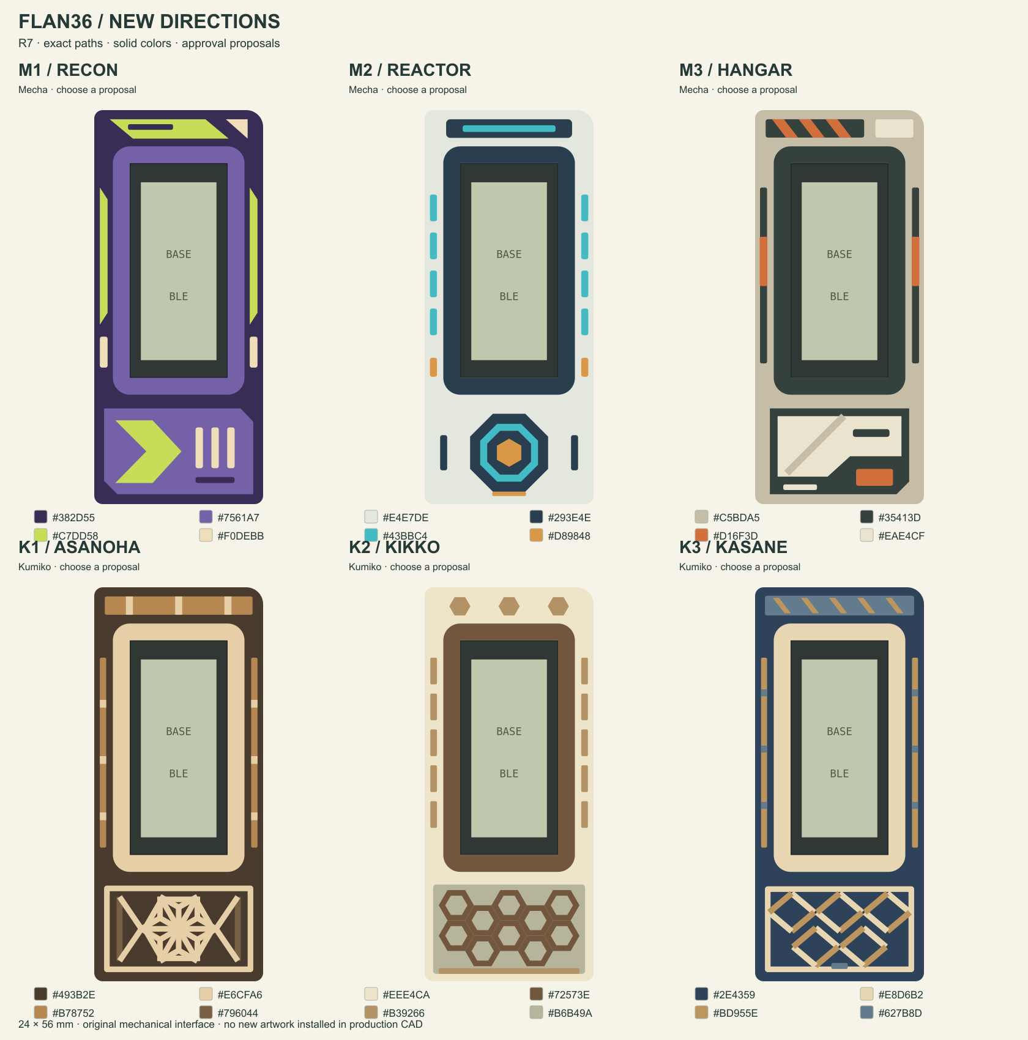
design/proposals/frame-redesign-r7/collection.png
