eduarbo/flan36/design/proposals/frame-redesign-r7/hanafuda-card.png

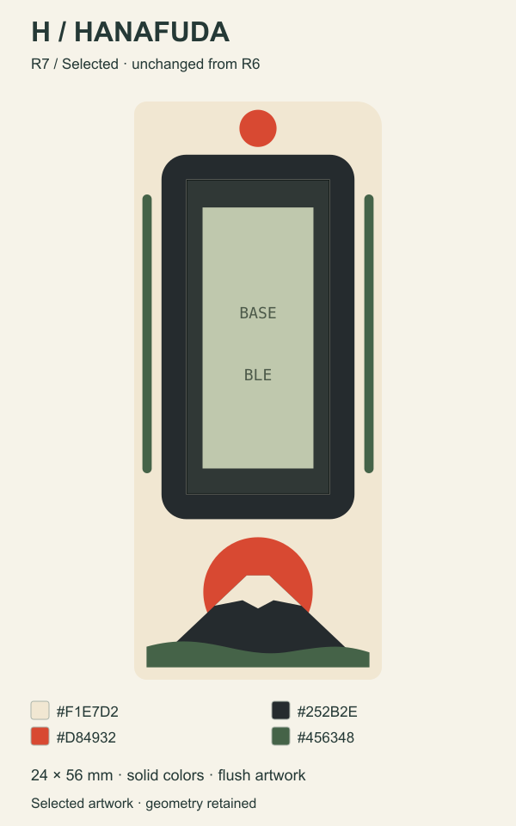
design/proposals/frame-redesign-r7/hanafuda-card.png
