eduarbo/flan36/design/proposals/frame-redesign-r7/hanafuda-dimensioned.png

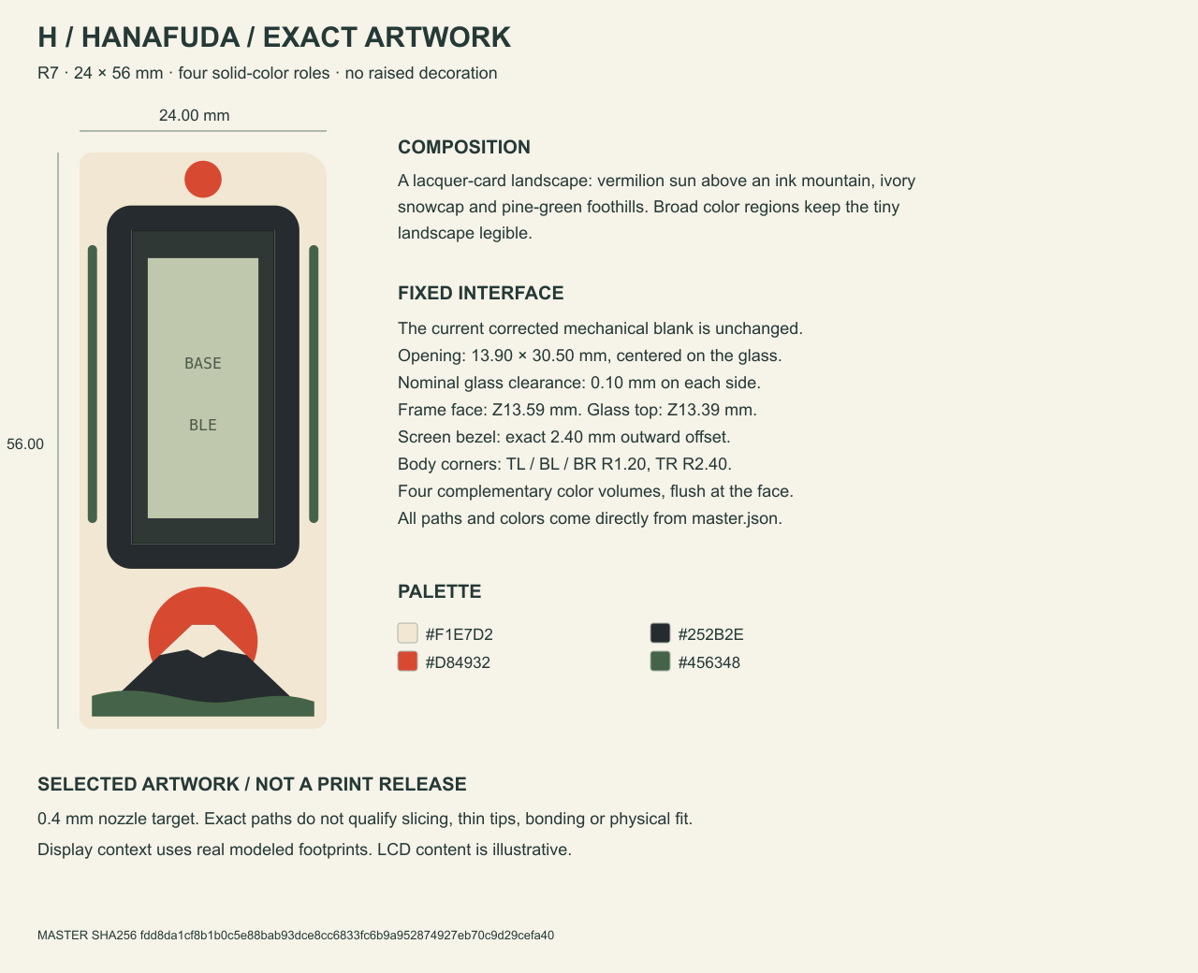
design/proposals/frame-redesign-r7/hanafuda-dimensioned.png
