eduarbo/flan36/design/proposals/frame-redesign-r7/kumiko-asanoha-card.png

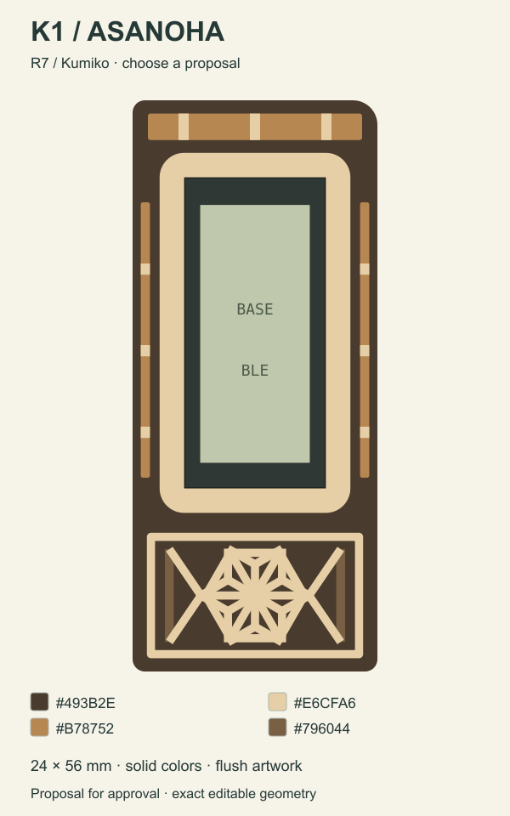
design/proposals/frame-redesign-r7/kumiko-asanoha-card.png
