eduarbo/flan36/design/proposals/frame-redesign-r7/kumiko.png

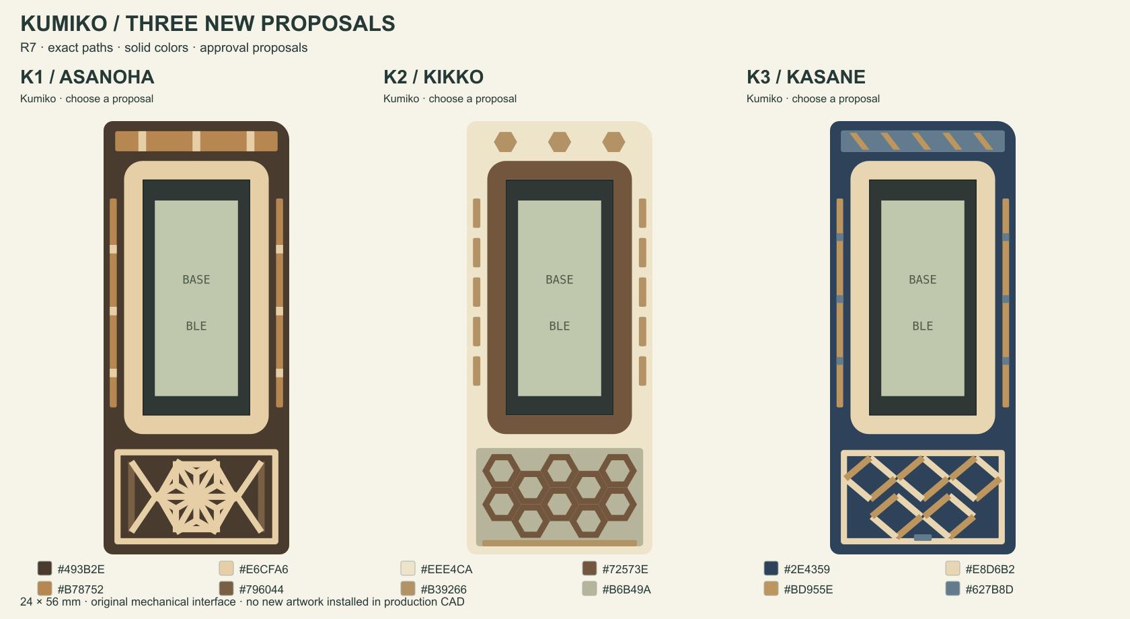
design/proposals/frame-redesign-r7/kumiko.png
