eduarbo/flan36/design/proposals/frame-redesign-r7/mecha-hangar-card.png

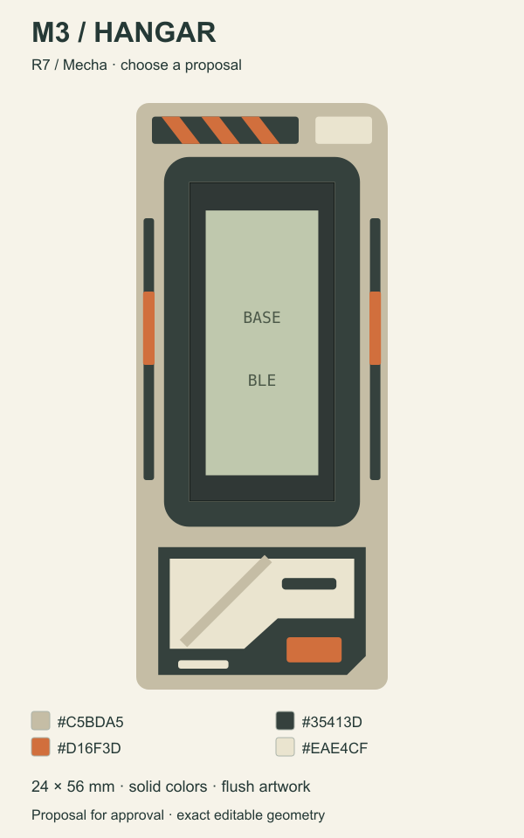
design/proposals/frame-redesign-r7/mecha-hangar-card.png
