eduarbo/flan36/design/proposals/frame-redesign-r7/mecha-recon-card.png

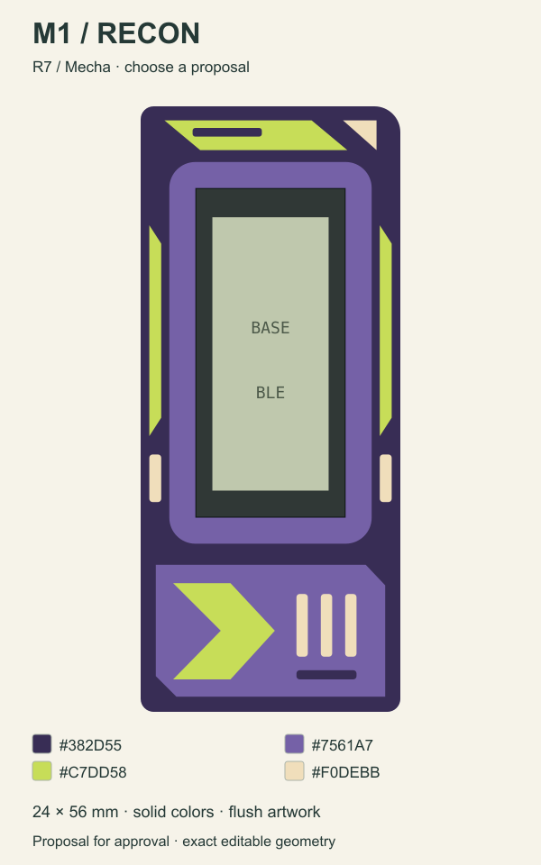
design/proposals/frame-redesign-r7/mecha-recon-card.png
