eduarbo/flan36/design/proposals/frame-redesign-r8/collection.png

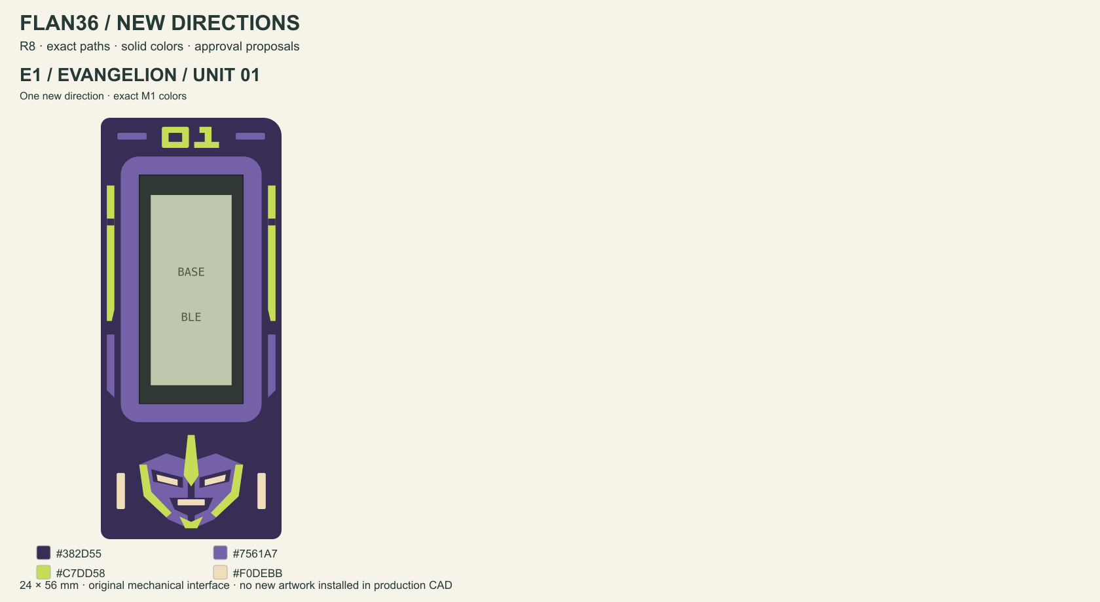
design/proposals/frame-redesign-r8/collection.png
