eduarbo/flan36/design/proposals/frame-redesign-r8/evangelion-dimensioned.png

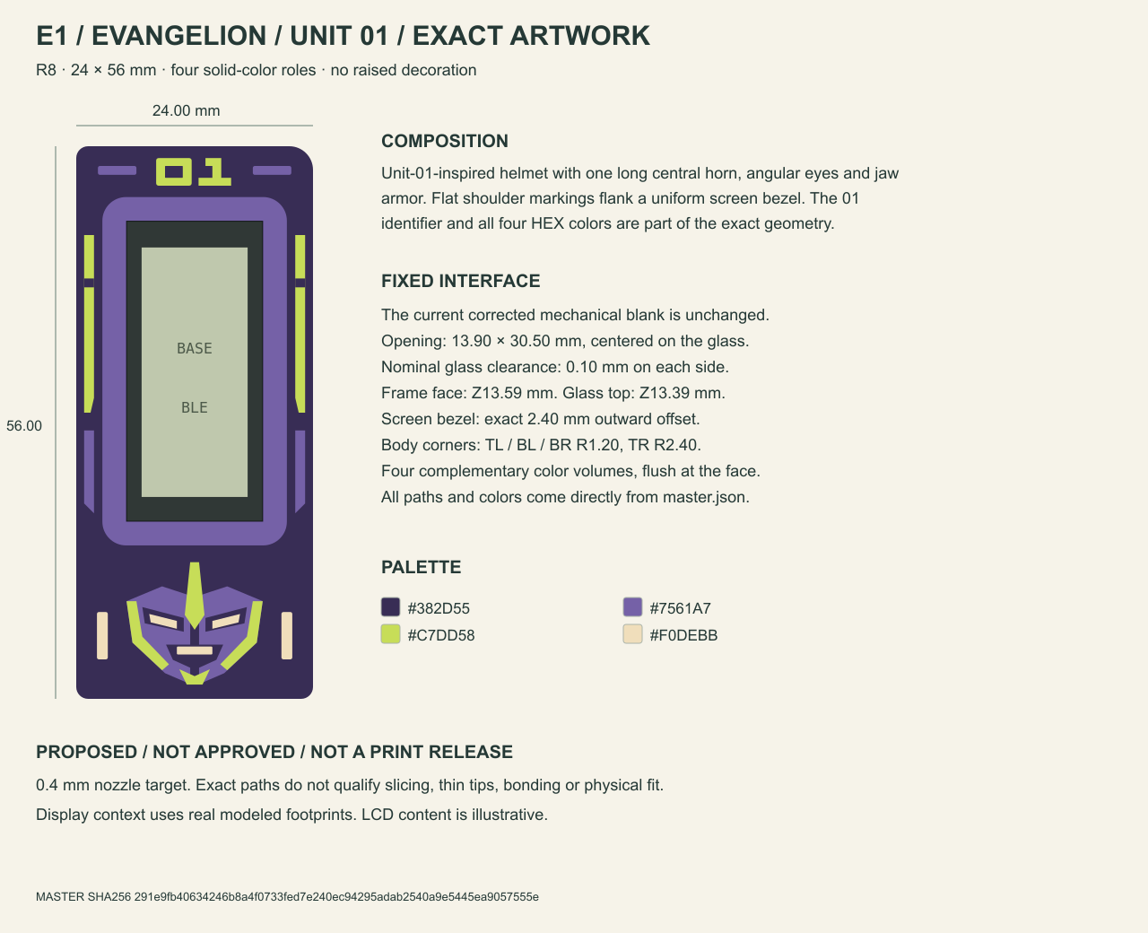
design/proposals/frame-redesign-r8/evangelion-dimensioned.png
