eduarbo/flan36/design/proposals/frame-redesign-r8/evangelion.png

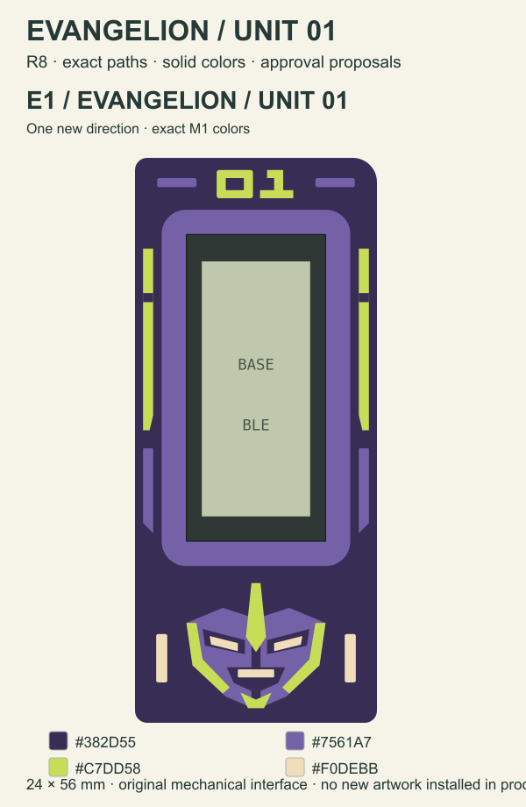
design/proposals/frame-redesign-r8/evangelion.png
