eduarbo/flan36/design/proposals/frame-redesign-r8/native-review.png

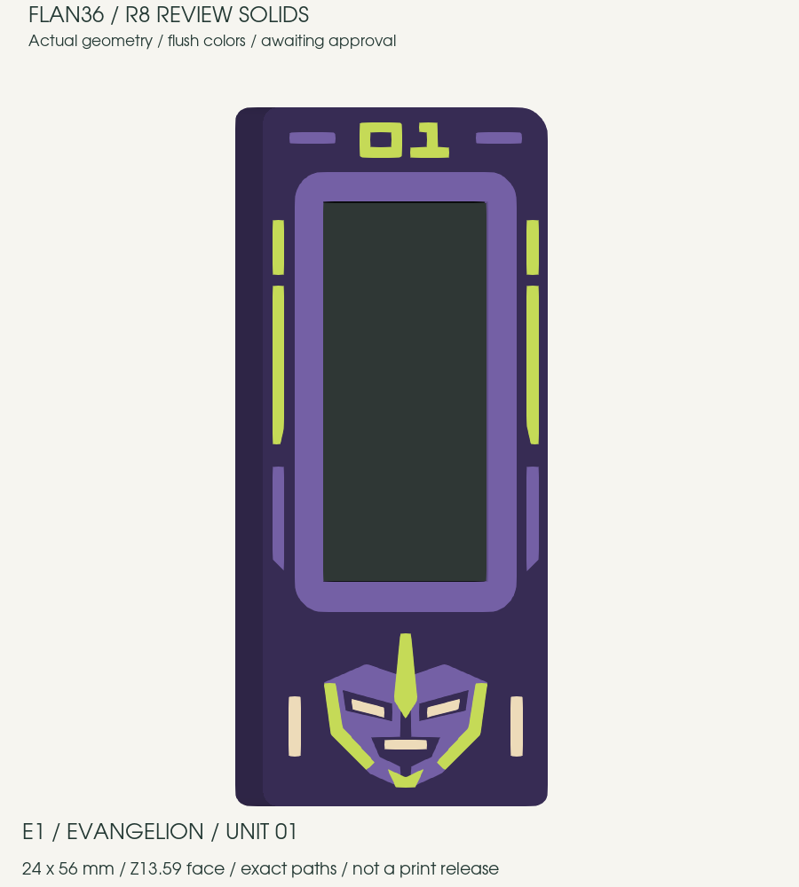
design/proposals/frame-redesign-r8/native-review.png
