eduarbo/flan36/design/proposals/frame-redesign-r8/snes-card.png

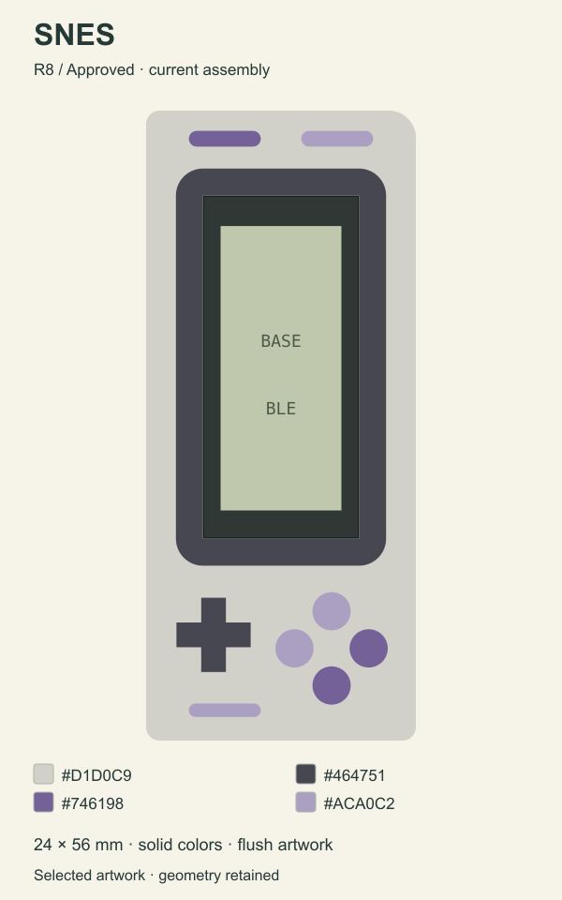
design/proposals/frame-redesign-r8/snes-card.png
