eduarbo/flan36/design/references/frame-concepts/caramel.png

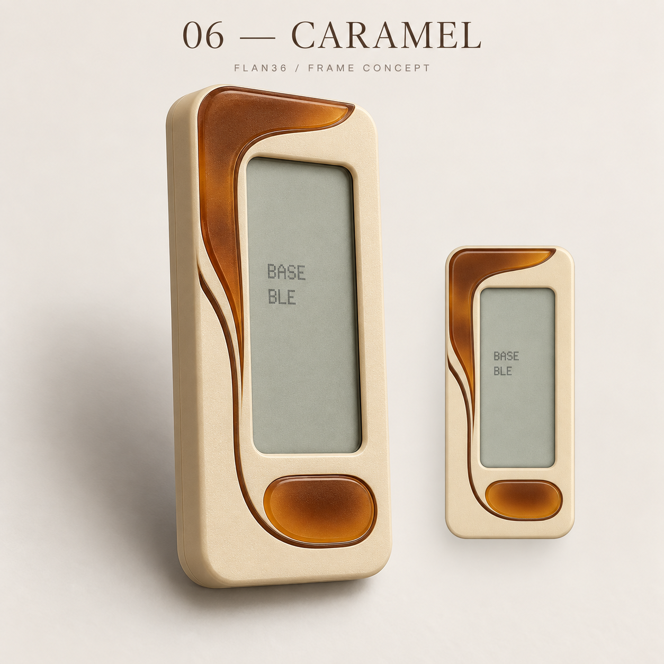
design/references/frame-concepts/caramel.png
