eduarbo/flan36/docs/frame-proposals/collection-a.png

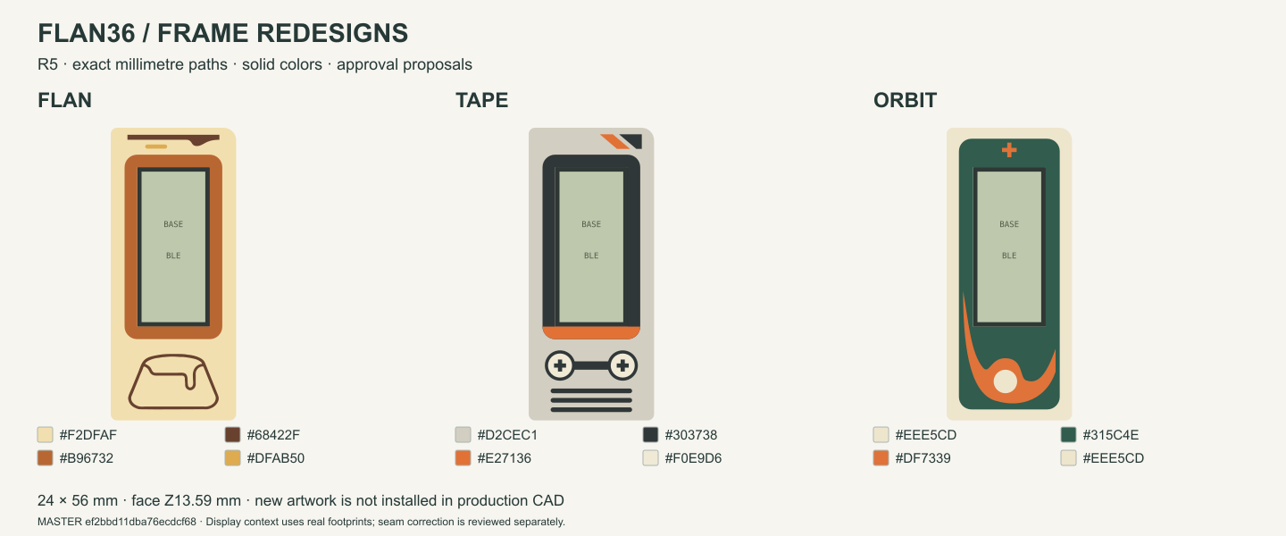
docs/frame-proposals/collection-a.png
