eduarbo/flan36/docs/frame-proposals/collection.png

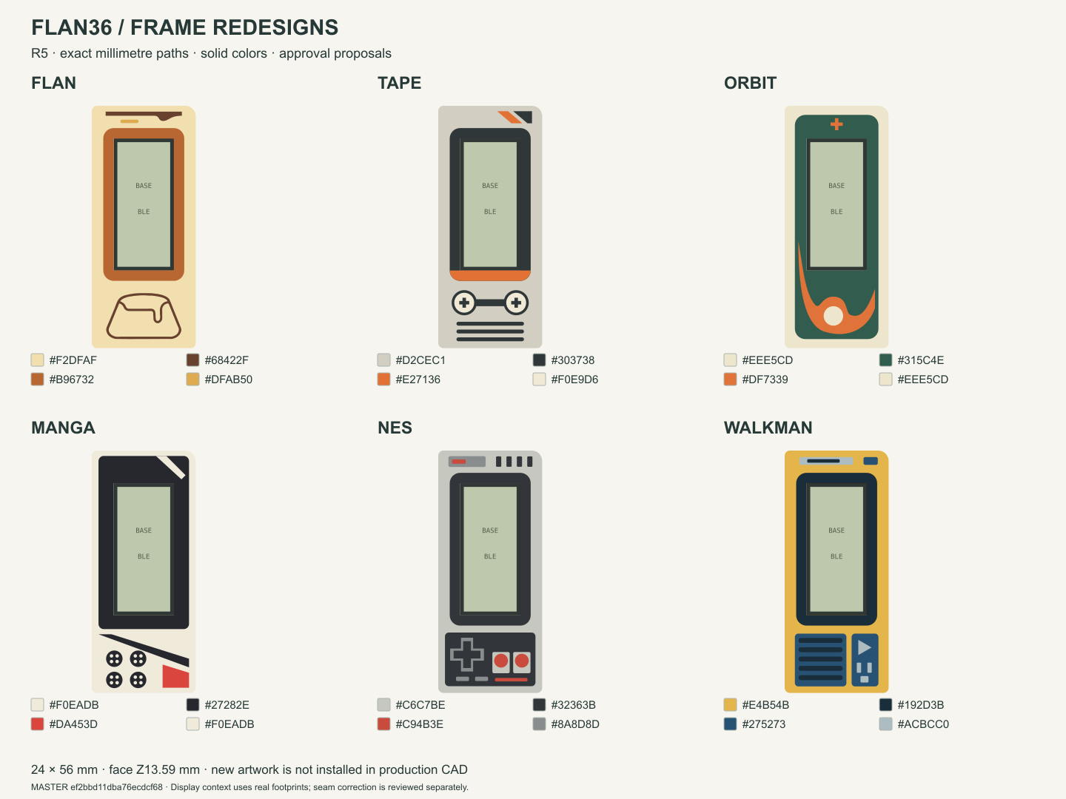
docs/frame-proposals/collection.png
