eduarbo/flan36/docs/frame-proposals/native-review.png

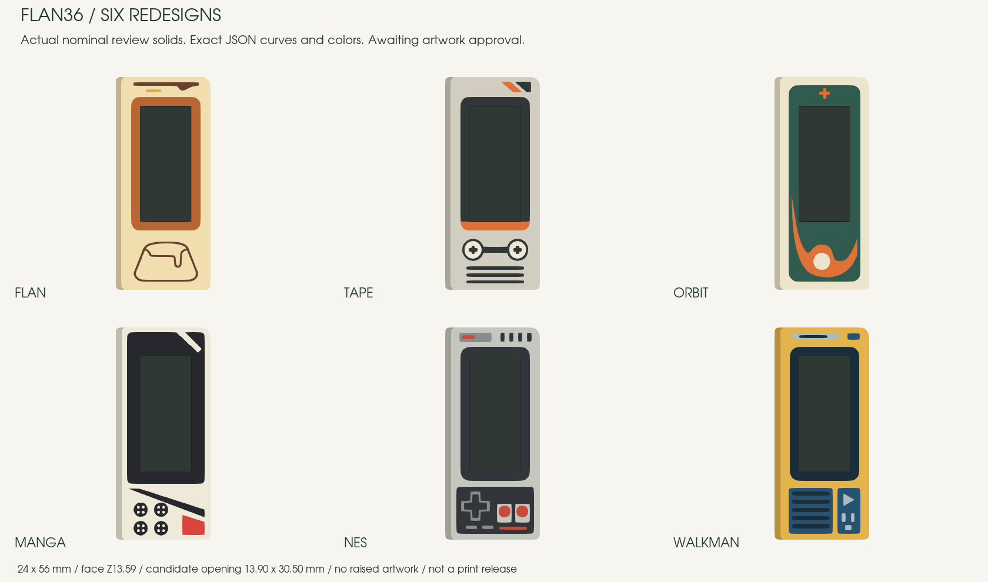
docs/frame-proposals/native-review.png
