eduarbo/flan36/docs/images/revI-detail.png

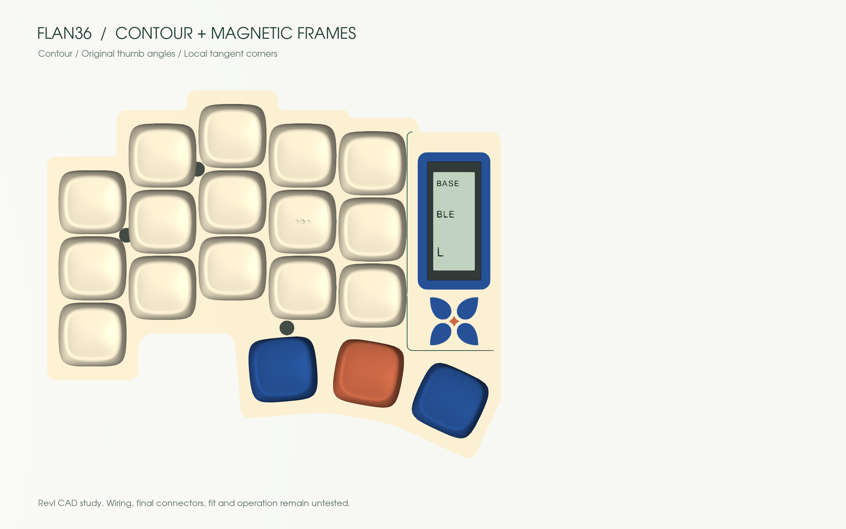
docs/images/revI-detail.png
