eduarbo/flan36/docs/images/revI-frames.png

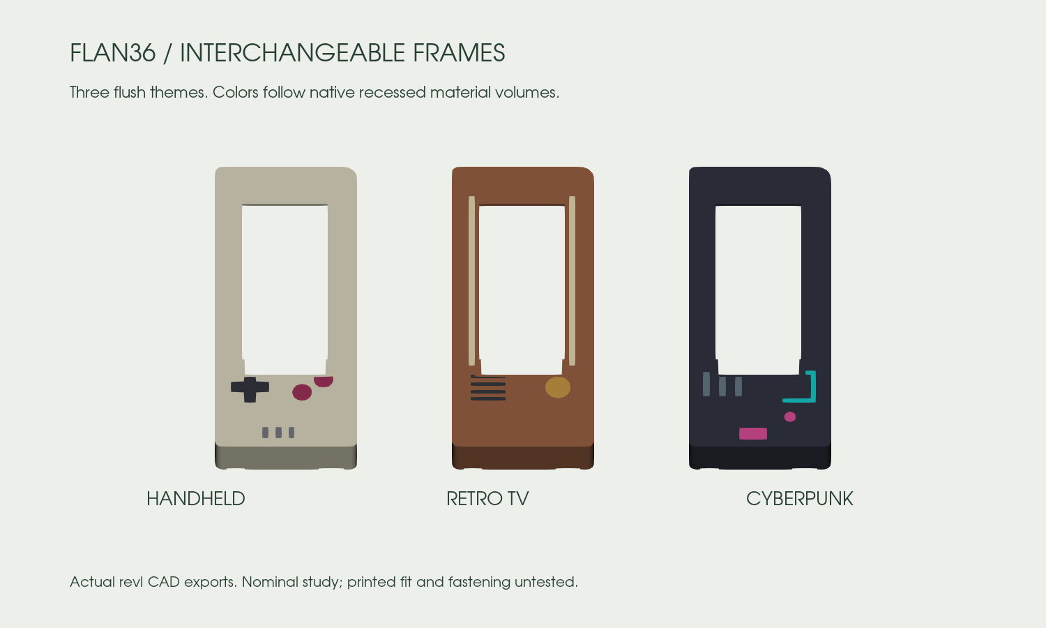
docs/images/revI-frames.png
