eduarbo/flan36/docs/images/viewer-canvas-compact.png

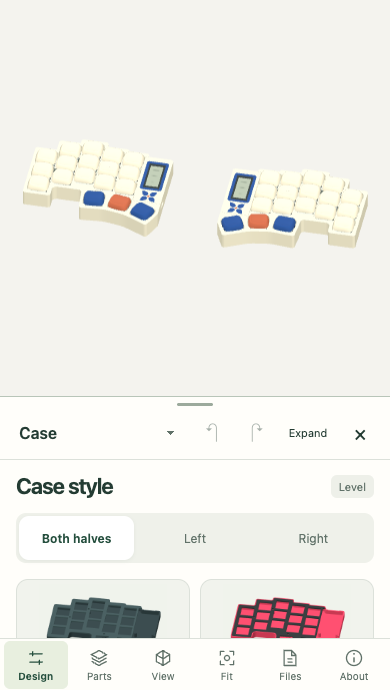
docs/images/viewer-canvas-compact.png
