eduarbo/flan36/docs/images/viewer-canvas-desktop.png

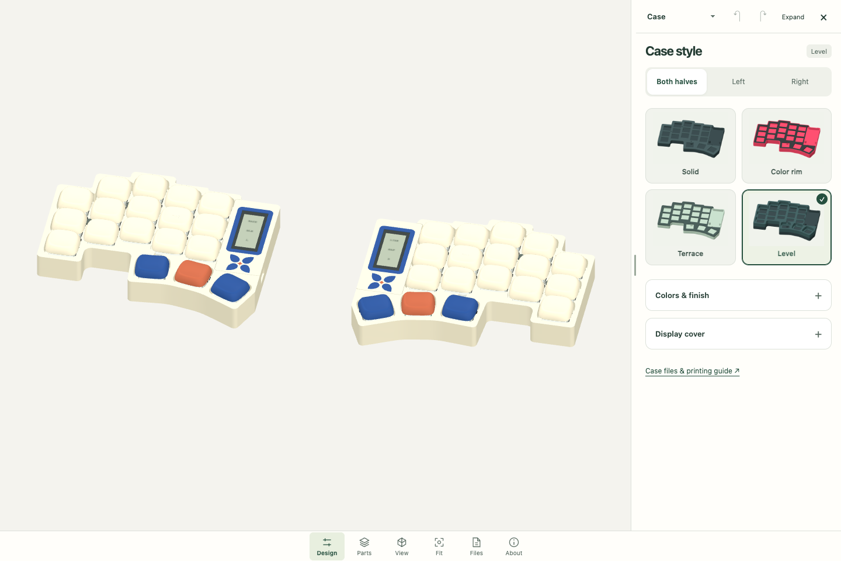
docs/images/viewer-canvas-desktop.png
