eduarbo/flan36/docs/images/viewer-canvas-expanded.png

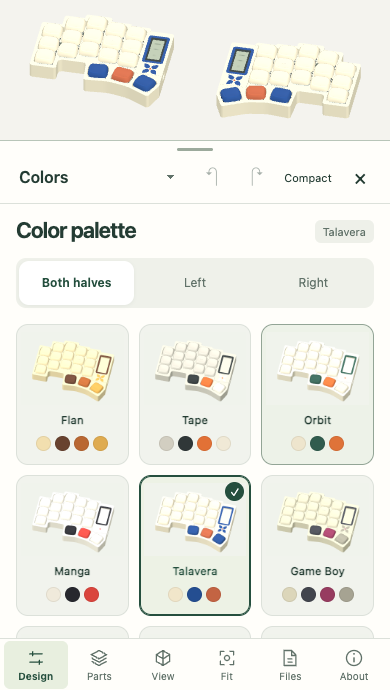
docs/images/viewer-canvas-expanded.png
