eduarbo/flan36/docs/images/viewer-canvas-mobile.png

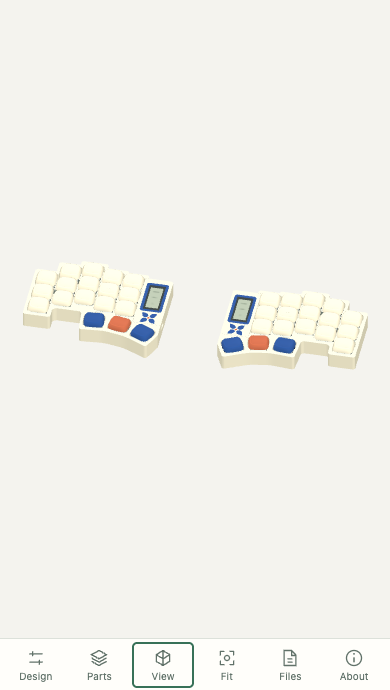
docs/images/viewer-canvas-mobile.png
