eduarbo/flan36/docs/images/viewer-mobile-about.png

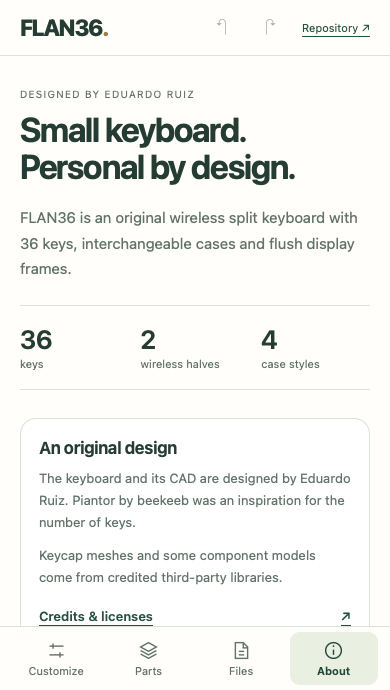
docs/images/viewer-mobile-about.png
