eduarbo/flan36/docs/images/viewer-mobile-customize.png

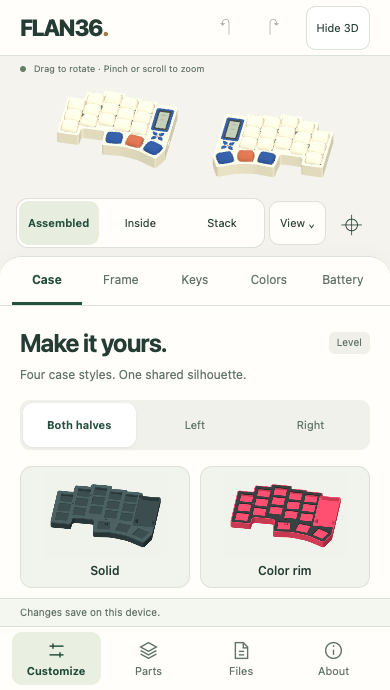
docs/images/viewer-mobile-customize.png
