eduarbo/flan36/docs/images/viewer-mobile-files.png

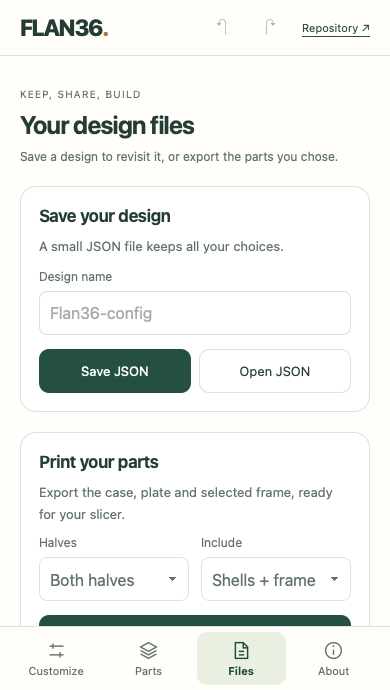
docs/images/viewer-mobile-files.png
