eduarbo/flan36/docs/images/viewer-mobile-inspect.png

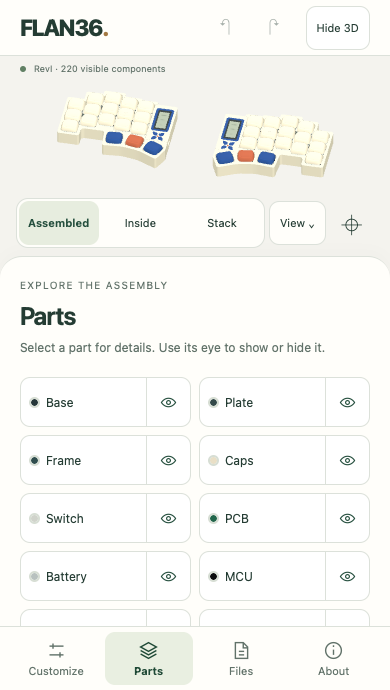
docs/images/viewer-mobile-inspect.png
