eduarbo/flan36/docs/images/viewer-mobile-licenses.png

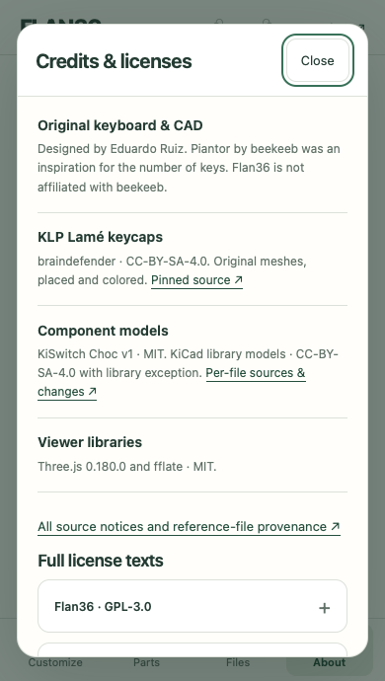
docs/images/viewer-mobile-licenses.png
