eduarbo/flan36/docs/images/viewer-redesign-desktop.png

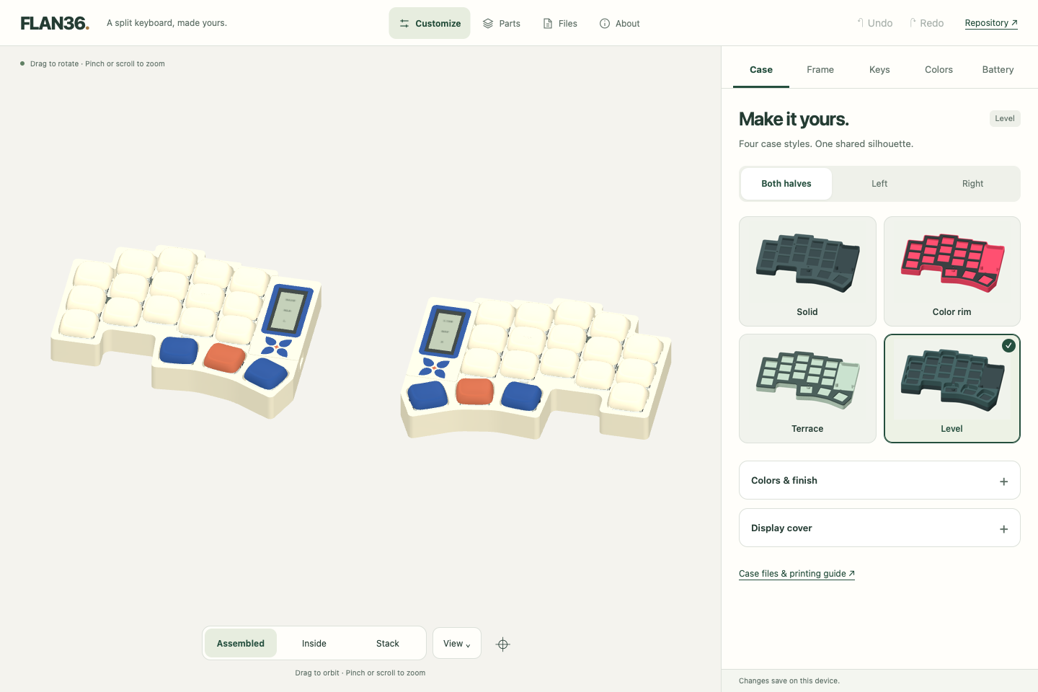
docs/images/viewer-redesign-desktop.png
