eduarbo/flan36/docs/images/viewer-responsive-desktop.png

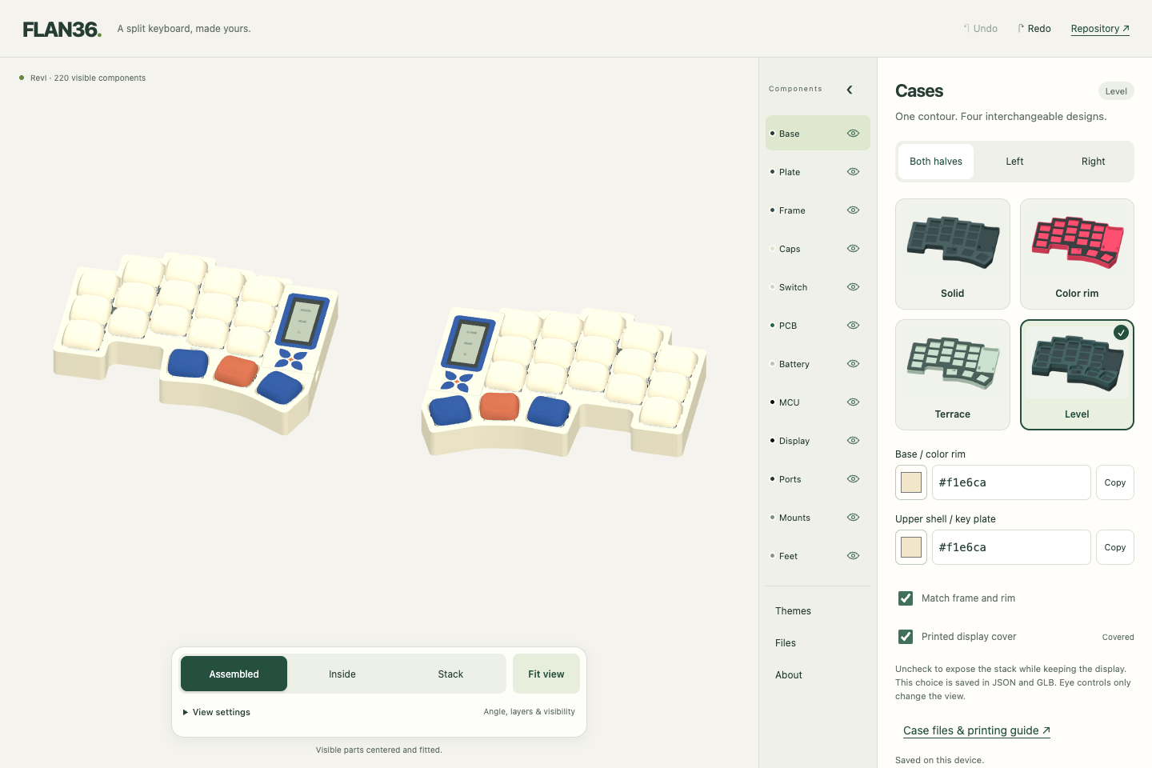
docs/images/viewer-responsive-desktop.png
