eduarbo/flan36/docs/images/viewer-responsive-mobile.png

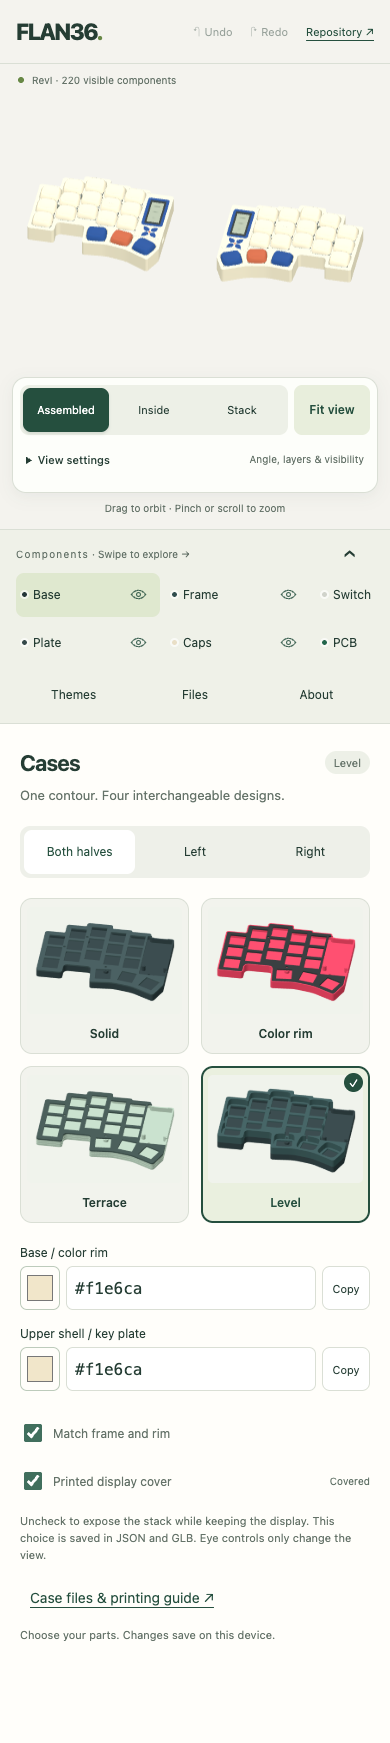
docs/images/viewer-responsive-mobile.png
