eduarbo/flan36/mechanical/revI/right-frame-hanafuda-detail.step

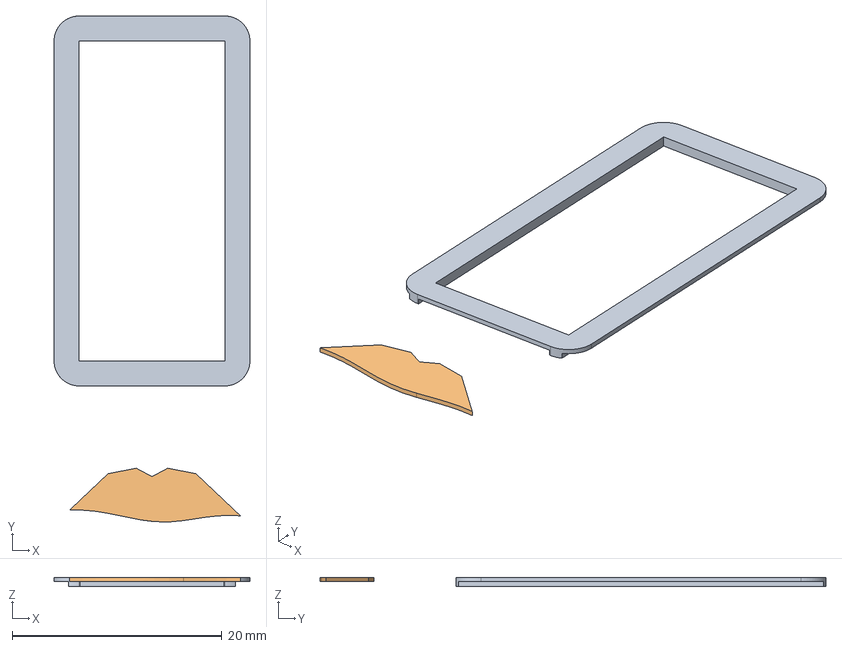
[picture p93: CAD file, 2026-10-08]
mechanical/revI/right-frame-hanafuda-detail.step
18.7 x 48.3 x 0.865 mm
