eduarbo/flan36/mechanical/revI/left-case-solid-base.step

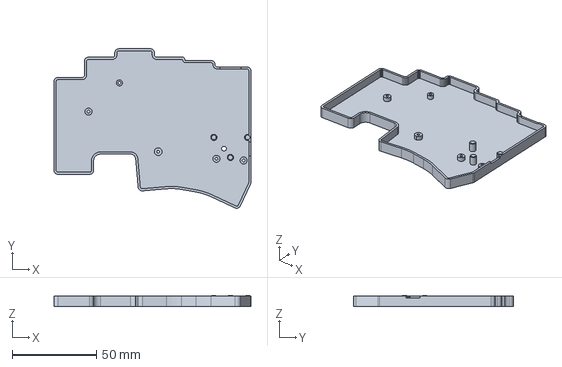
[picture p94: CAD file, 2026-10-08]
mechanical/revI/left-case-solid-base.step
116.8 x 94.6 x 6.60 mm
