eduarbo/flan36/hardware/revI/models/choc-envelope.step

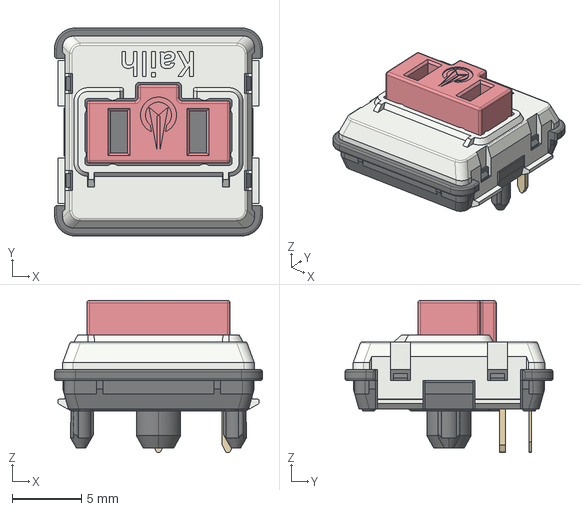
[picture p95: CAD file, 2026-09-28]
hardware/revI/models/choc-envelope.step
15.0 x 15.0 x 11.0 mm
