eduarbo/flan36/mechanical/revI/right-frame-ipod-body.step

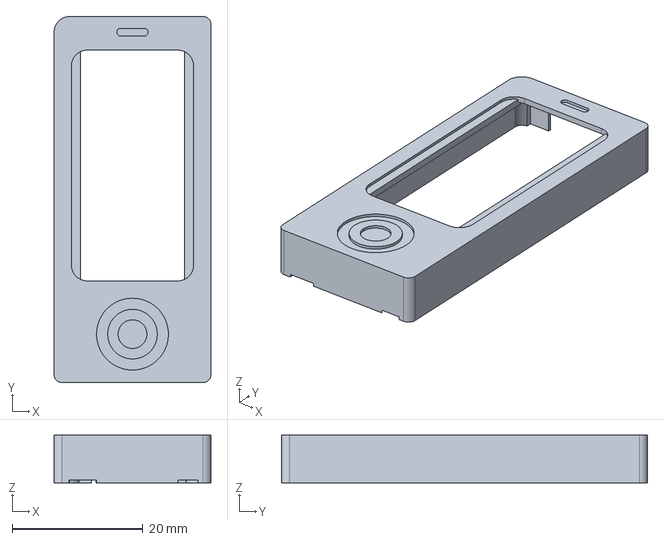
[picture p96: CAD file, 2026-10-08]
mechanical/revI/right-frame-ipod-body.step
24.0 x 56.0 x 7.29 mm
