eduarbo/flan36/hardware/revI/models/left-slider.step

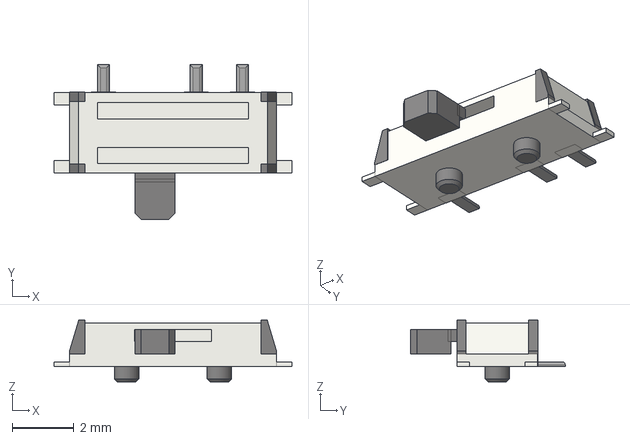
[picture p97: CAD file, 2026-09-28]
hardware/revI/models/left-slider.step
7.70 x 5.00 x 2.00 mm
