eduarbo/flan36/mechanical/revI/left-frame-gameboy.step

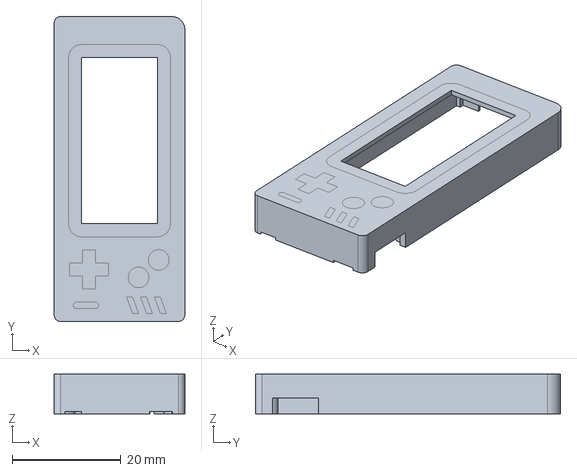
[picture p98: CAD file, 2026-10-08]
mechanical/revI/left-frame-gameboy.step
24.0 x 56.0 x 7.29 mm
