eduarbo/flan36/mechanical/revI/right-frame-snes-secondary.step

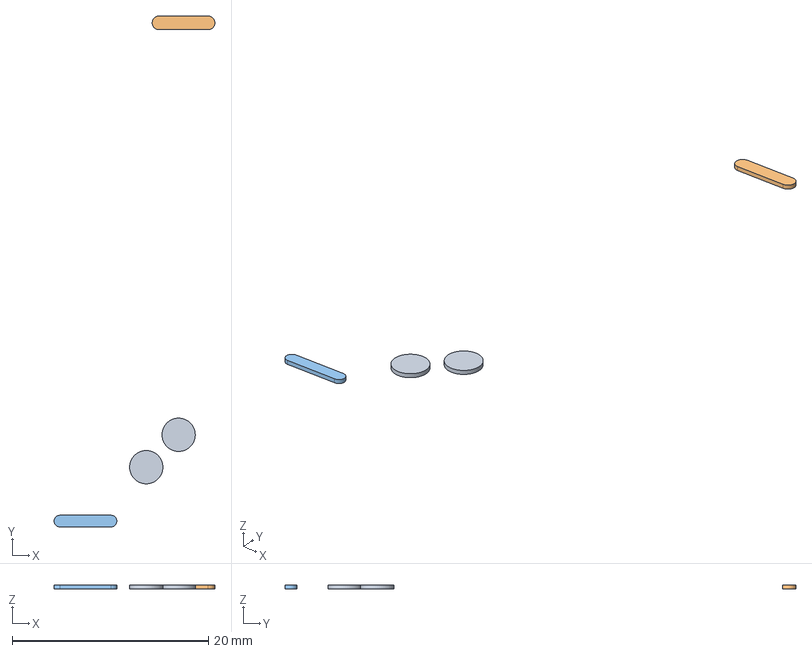
[picture p99: CAD file, 2026-10-08]
mechanical/revI/right-frame-snes-secondary.step
16.4 x 52.1 x 0.4 mm
