eduarbo/flan36/hardware/revI/models/left-mcu.step

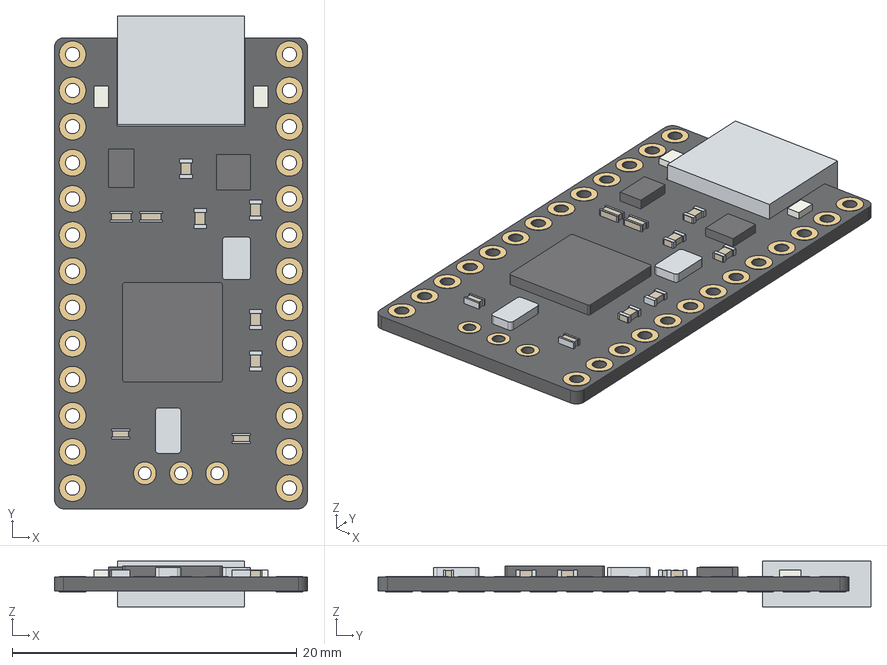
[picture p100: CAD file, 2026-09-28]
hardware/revI/models/left-mcu.step
17.8 x 34.6 x 3.20 mm
