eduarbo/flan36/hardware/revI/models/right-reset.step

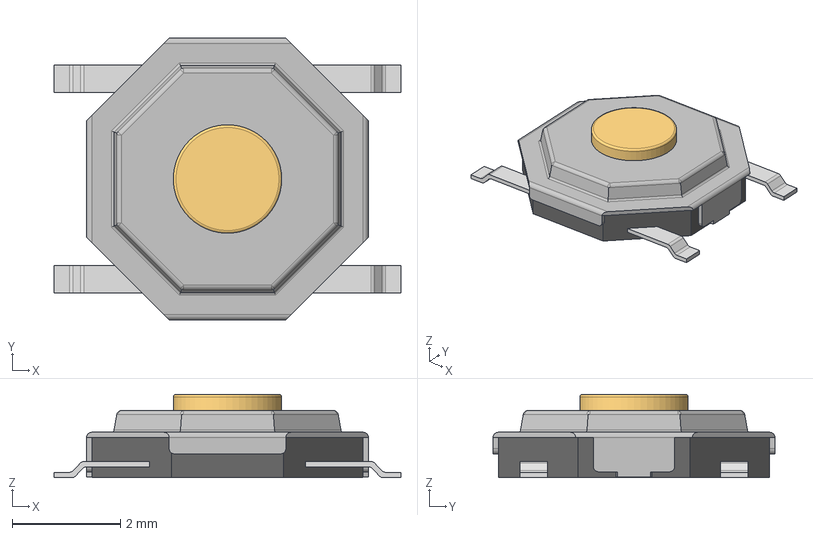
[picture p101: CAD file, 2026-09-28]
hardware/revI/models/right-reset.step
6.40 x 5.20 x 1.54 mm
