eduarbo/flan36/mechanical/revI/left-frame-gameboy-accent.step

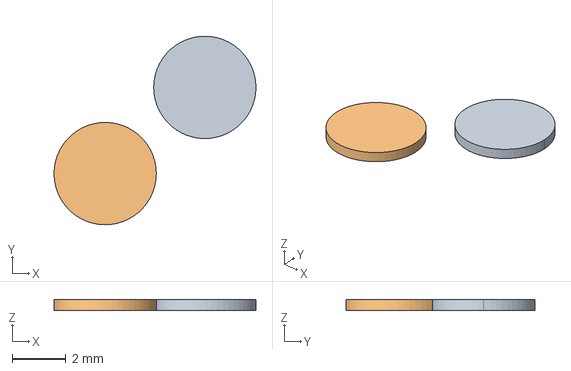
[picture p102: CAD file, 2026-10-08]
mechanical/revI/left-frame-gameboy-accent.step
7.50 x 7.00 x 0.4 mm
