eduarbo/flan36/mechanical/revI/right-diodes.stl

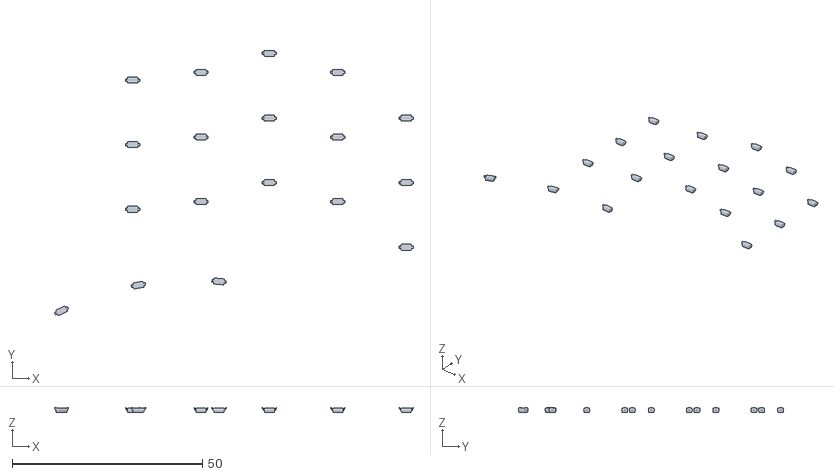
[picture p103: CAD file, 2026-10-08]
mechanical/revI/right-diodes.stl
94.4 x 69.8 x 1.26
