eduarbo/flan36/mechanical/revI/right-frame-gameboy-detail.step

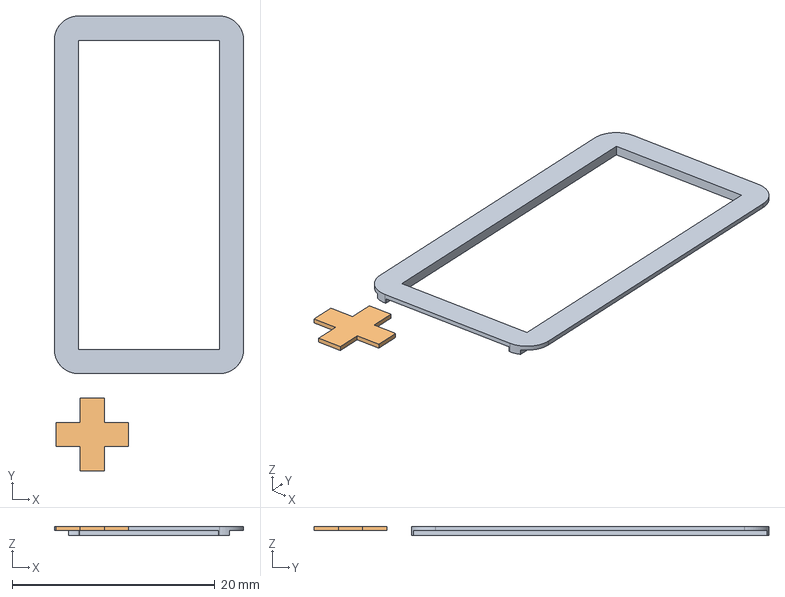
[picture p104: CAD file, 2026-10-08]
mechanical/revI/right-frame-gameboy-detail.step
18.7 x 44.9 x 0.865 mm
