eduarbo/flan36/mechanical/revI/component-hotswap-1.stl

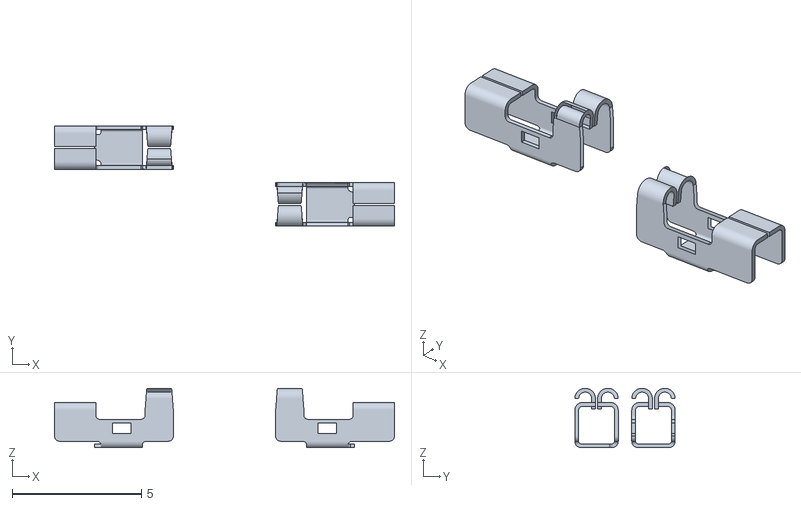
[picture p105: CAD file, 2026-10-08]
mechanical/revI/component-hotswap-1.stl
13.1 x 3.88 x 2.30
