eduarbo/flan36/mechanical/revI/right-diodes-visual-2.stl

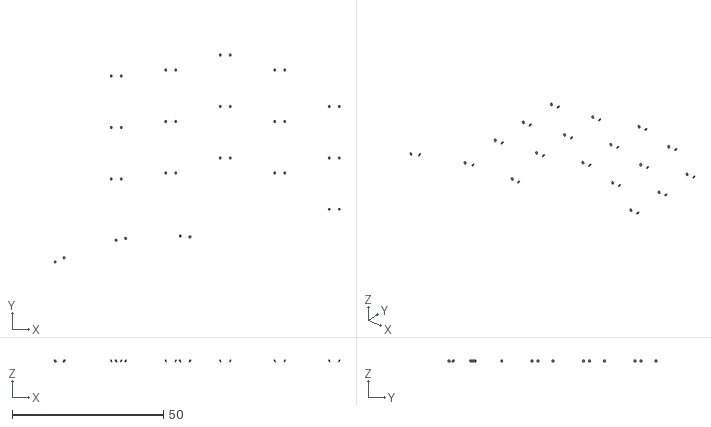
[picture p106: CAD file, 2026-10-08]
mechanical/revI/right-diodes-visual-2.stl
94.4 x 69.1 x 0.775
