eduarbo/flan36/mechanical/revI/left-case-rim-base.step

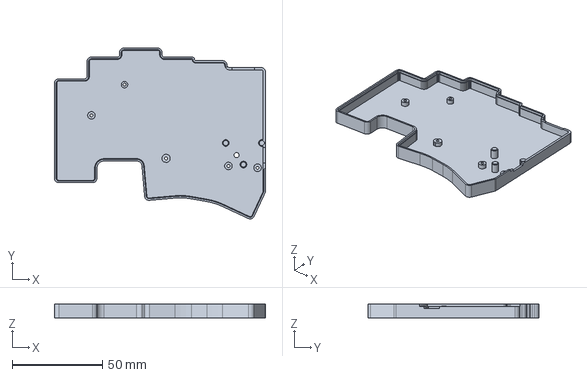
[picture p107: CAD file, 2026-10-08]
mechanical/revI/left-case-rim-base.step
116.8 x 94.6 x 7.60 mm
