eduarbo/flan36/mechanical/revI/left-frame-gameboy-secondary.step

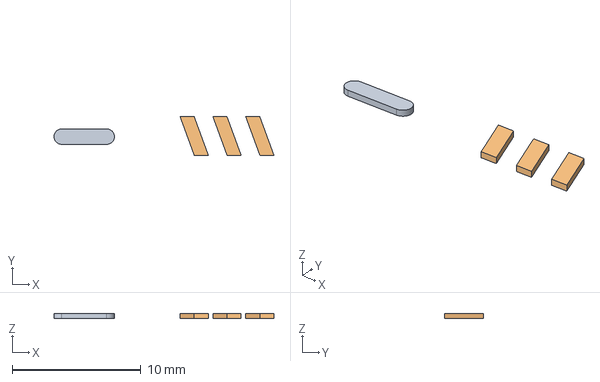
[picture p108: CAD file, 2026-10-08]
mechanical/revI/left-frame-gameboy-secondary.step
17.1 x 3.00 x 0.4 mm
