eduarbo/flan36/mechanical/revI/left-frame-talavera-accent.step

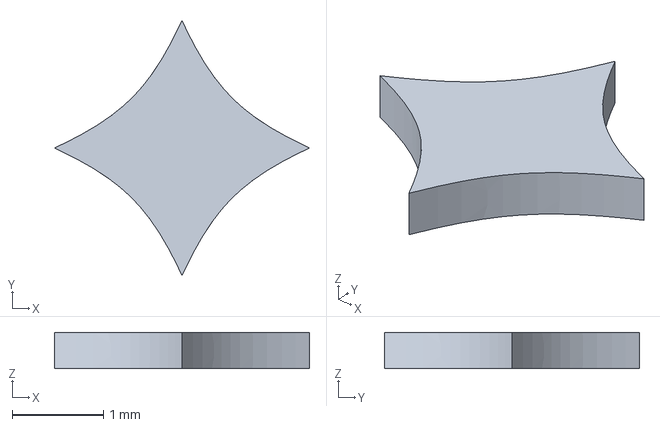
[picture p109: CAD file, 2026-10-08]
mechanical/revI/left-frame-talavera-accent.step
2.80 x 2.80 x 0.4 mm
