eduarbo/flan36/mechanical/revI/right-frame-talavera-secondary.step

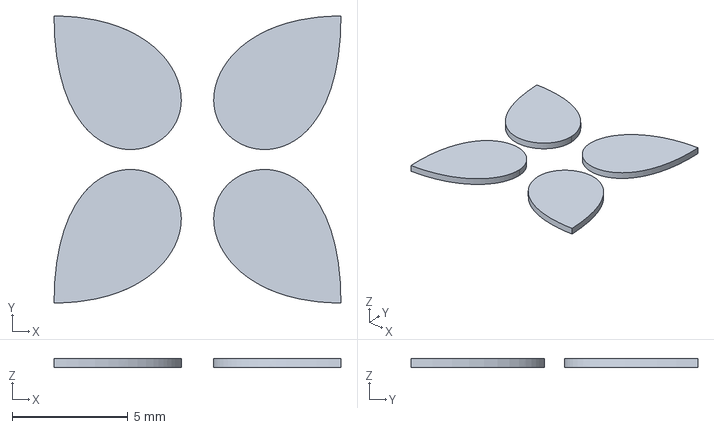
[picture p110: CAD file, 2026-10-08]
mechanical/revI/right-frame-talavera-secondary.step
12.4 x 12.4 x 0.4 mm
