eduarbo/flan36/mechanical/revI/left-frame-ipod-accent.step

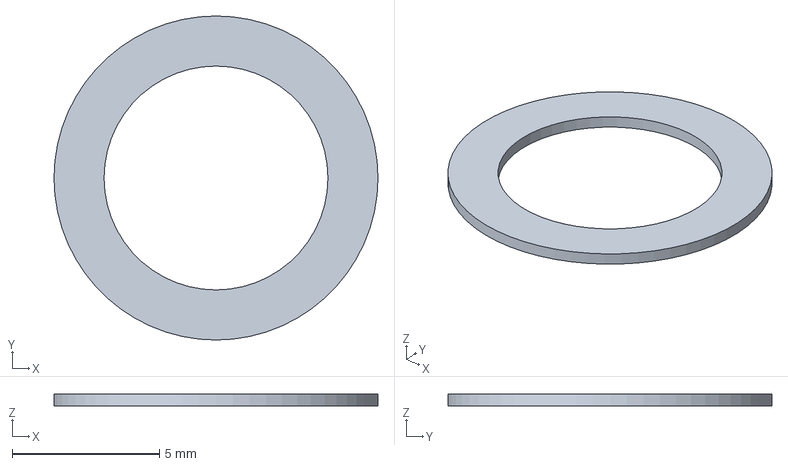
[picture p111: CAD file, 2026-10-08]
mechanical/revI/left-frame-ipod-accent.step
11.0 x 11.0 x 0.4 mm
