eduarbo/flan36/mechanical/revI/left-frame-snes-accent.step

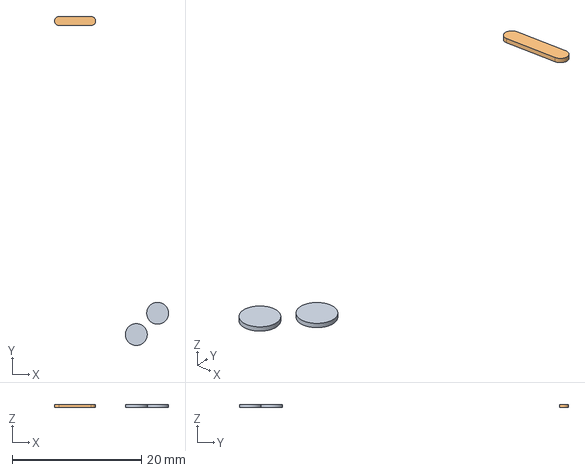
[picture p112: CAD file, 2026-10-08]
mechanical/revI/left-frame-snes-accent.step
17.7 x 51.0 x 0.4 mm
