eduarbo/flan36/mechanical/revI/left-frame-ipod-secondary.step

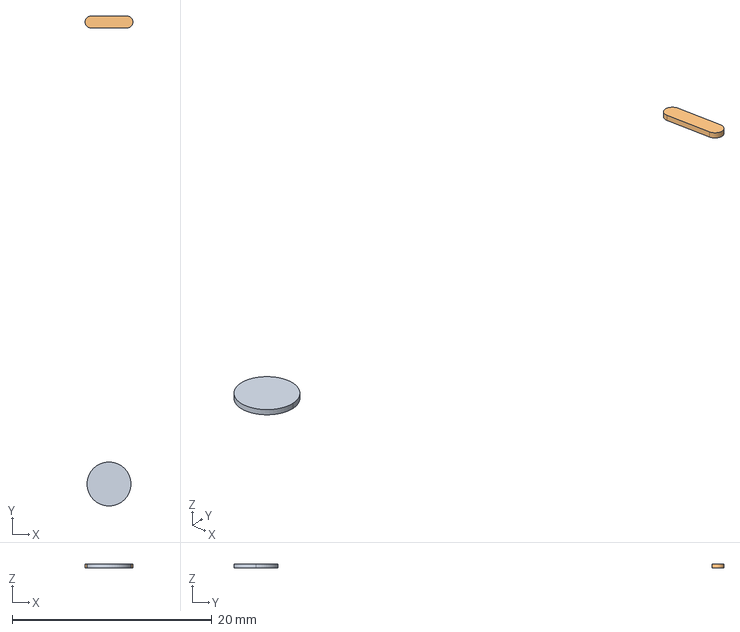
[picture p113: CAD file, 2026-10-08]
mechanical/revI/left-frame-ipod-secondary.step
4.80 x 49.0 x 0.4 mm
