eduarbo/flan36/mechanical/revI/right-frame-phone-secondary.step

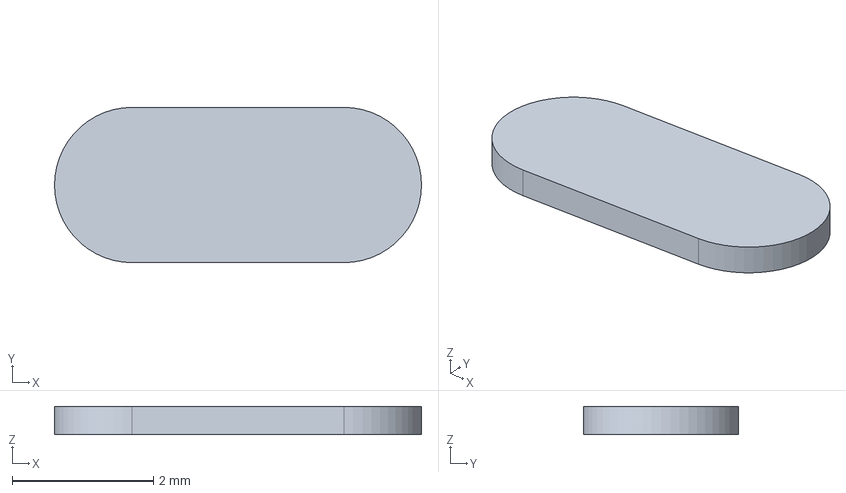
[picture p114: CAD file, 2026-10-08]
mechanical/revI/right-frame-phone-secondary.step
5.20 x 2.20 x 0.4 mm
