eduarbo/flan36/mechanical/revI/right-frame-phone-detail.step

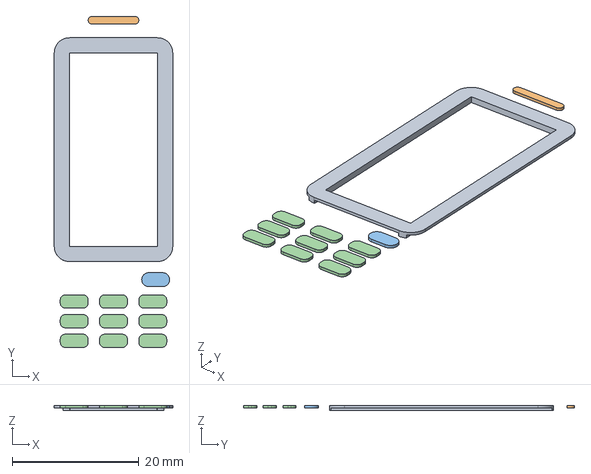
[picture p115: CAD file, 2026-10-08]
mechanical/revI/right-frame-phone-detail.step
18.7 x 52.2 x 0.865 mm
