eduarbo/flan36/mechanical/revI/right-hotswap-sockets-visual-1.stl

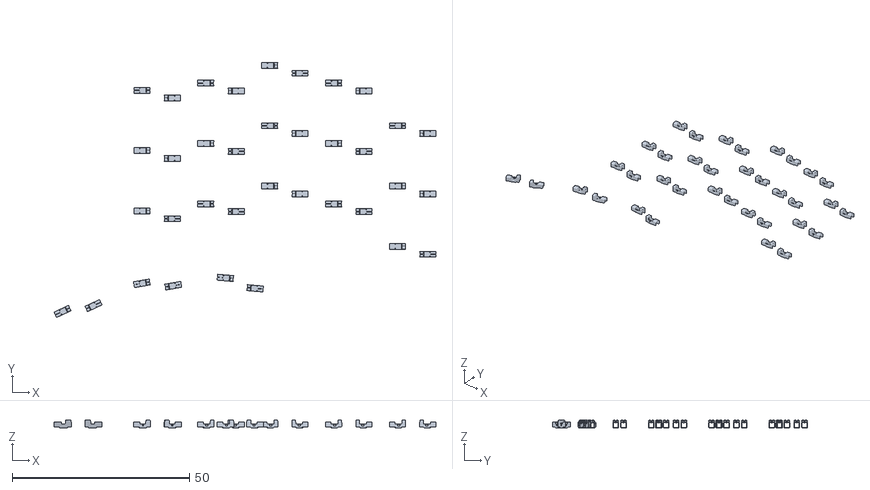
[picture p116: CAD file, 2026-10-08]
mechanical/revI/right-hotswap-sockets-visual-1.stl
107.6 x 71.9 x 2.30
