eduarbo/flan36/mechanical/revI/right-frame-hanafuda-accent.step

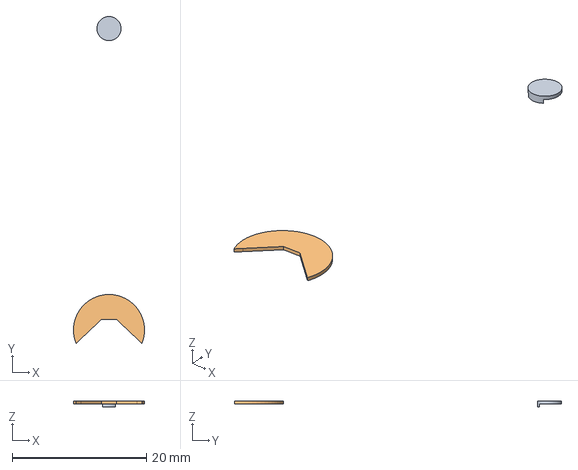
[picture p117: CAD file, 2026-10-08]
mechanical/revI/right-frame-hanafuda-accent.step
10.6 x 48.7 x 0.865 mm
