eduarbo/flan36/mechanical/revI/right-diodes-visual-0.stl

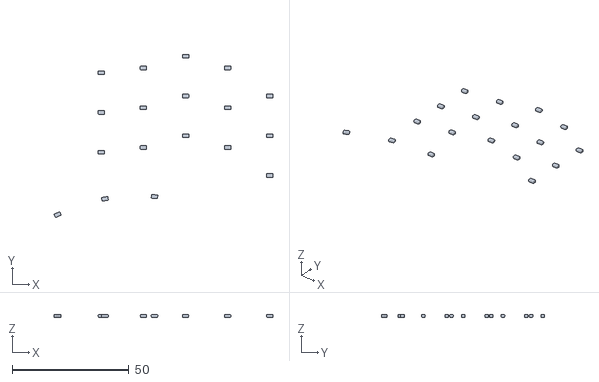
[picture p118: CAD file, 2026-10-08]
mechanical/revI/right-diodes-visual-0.stl
93.6 x 69.8 x 1.15
