eduarbo/flan36/mechanical/revI/left-frame-phone-accent.step

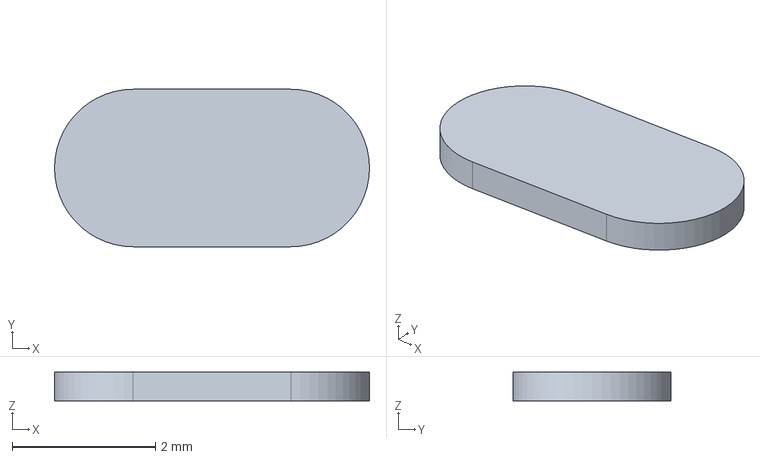
[picture p119: CAD file, 2026-10-08]
mechanical/revI/left-frame-phone-accent.step
4.40 x 2.20 x 0.4 mm
