eduarbo/flan36/mechanical/revI/left-diodes-visual-1.stl

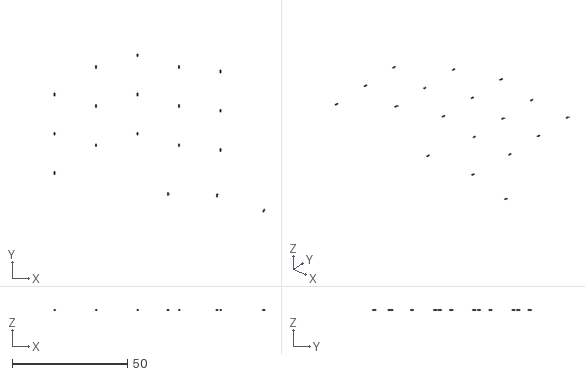
[picture p120: CAD file, 2026-10-08]
mechanical/revI/left-diodes-visual-1.stl
91.5 x 68.6 x 0.01
