eduarbo/flan36/mechanical/revI/component-hotswap-0.stl

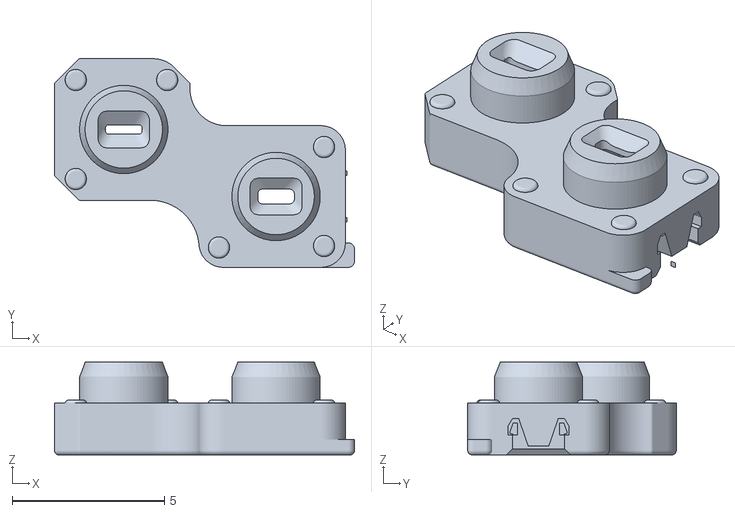
[picture p121: CAD file, 2026-10-08]
mechanical/revI/component-hotswap-0.stl
9.85 x 6.85 x 3.05
