eduarbo/flan36/mechanical/revI/left-frame-hanafuda-secondary.step

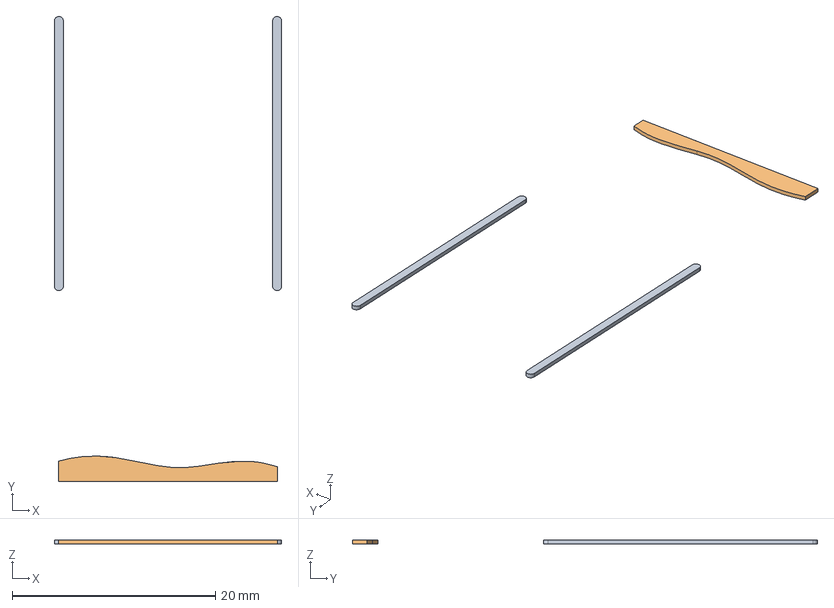
[picture p122: CAD file, 2026-10-08]
mechanical/revI/left-frame-hanafuda-secondary.step
22.4 x 45.8 x 0.4 mm
