eduarbo/flan36/mechanical/revI/left-hotswap-sockets-visual-1.stl

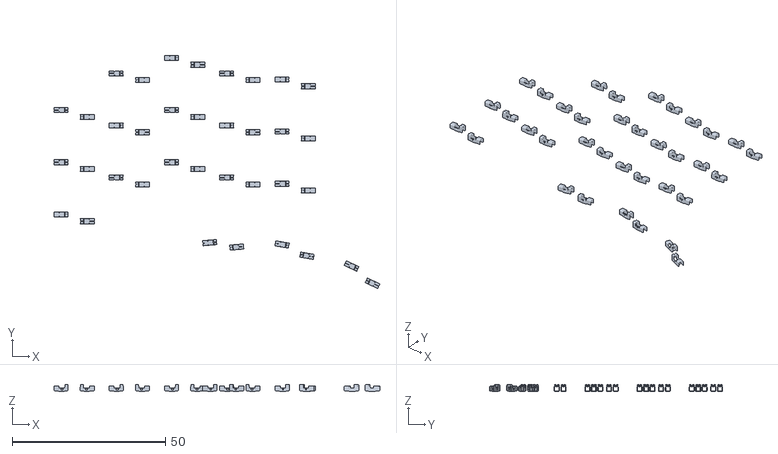
[picture p123: CAD file, 2026-10-08]
mechanical/revI/left-hotswap-sockets-visual-1.stl
106.2 x 76.0 x 2.30
