eduarbo/flan36/mechanical/revI/right-diodes-visual-1.stl

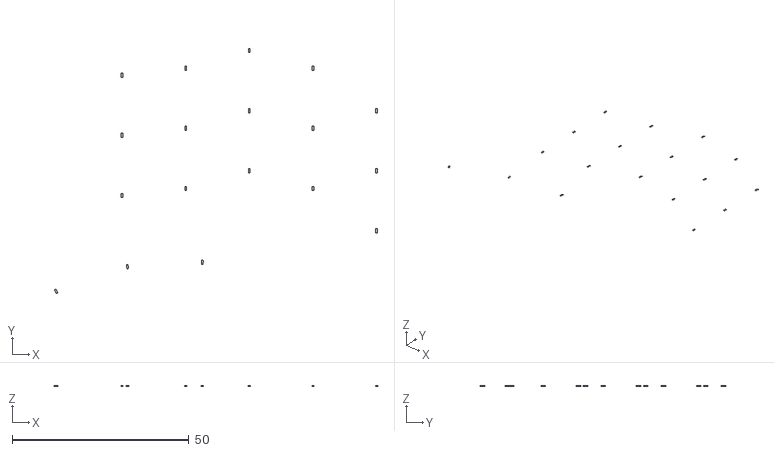
[picture p124: CAD file, 2026-10-08]
mechanical/revI/right-diodes-visual-1.stl
91.3 x 69.4 x 0.01
