eduarbo/flan36/mechanical/revI/right-frame-tape-secondary.step

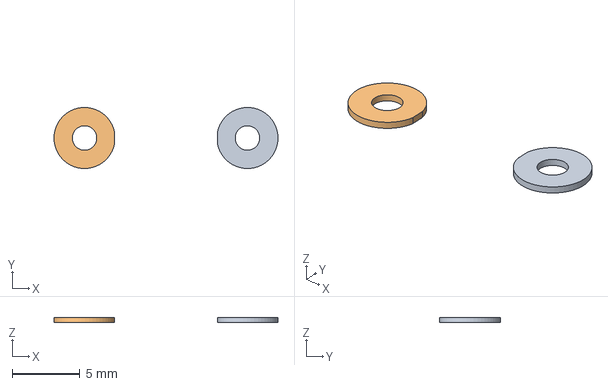
[picture p125: CAD file, 2026-09-29]
mechanical/revI/right-frame-tape-secondary.step
16.5 x 4.50 x 0.4 mm
