eduarbo/flan36/mechanical/revI/right-frame-flan-accent.step

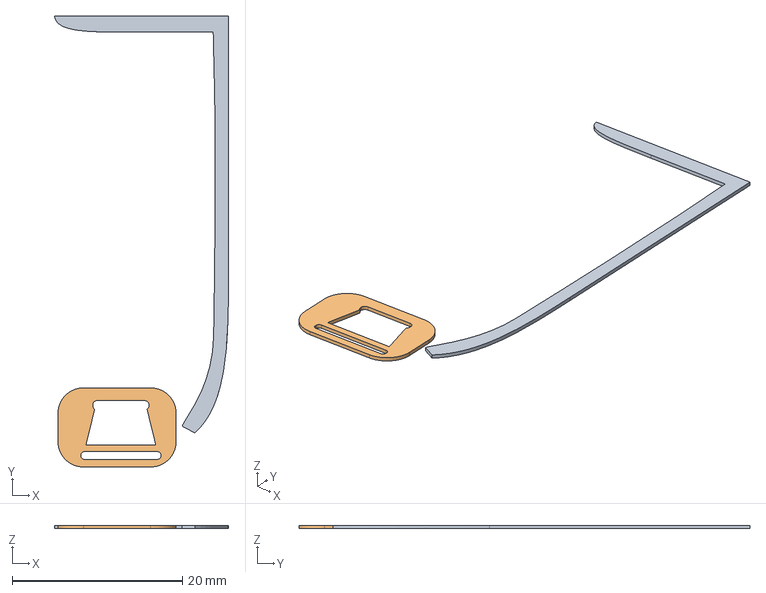
[picture p126: CAD file, 2026-09-29]
mechanical/revI/right-frame-flan-accent.step
20.4 x 53.0 x 0.4 mm
