eduarbo/flan36/mechanical/revI/left-frame-orbit-accent.step

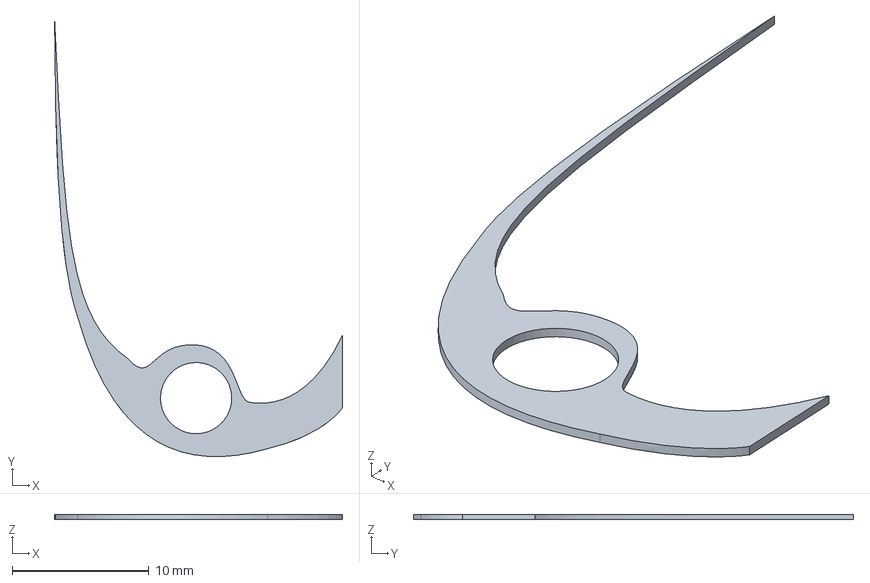
[picture p127: CAD file, 2026-09-29]
mechanical/revI/left-frame-orbit-accent.step
21.0 x 32.2 x 0.4 mm
