eduarbo/flan36/mechanical/revI/right-frame-tape-body.step

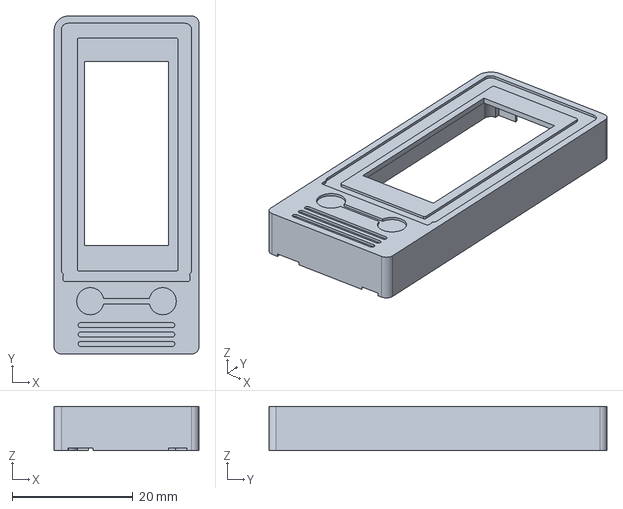
[picture p128: CAD file, 2026-09-29]
mechanical/revI/right-frame-tape-body.step
24.0 x 56.0 x 7.29 mm
