eduarbo/flan36/mechanical/revI/left-frame-nes-secondary.step

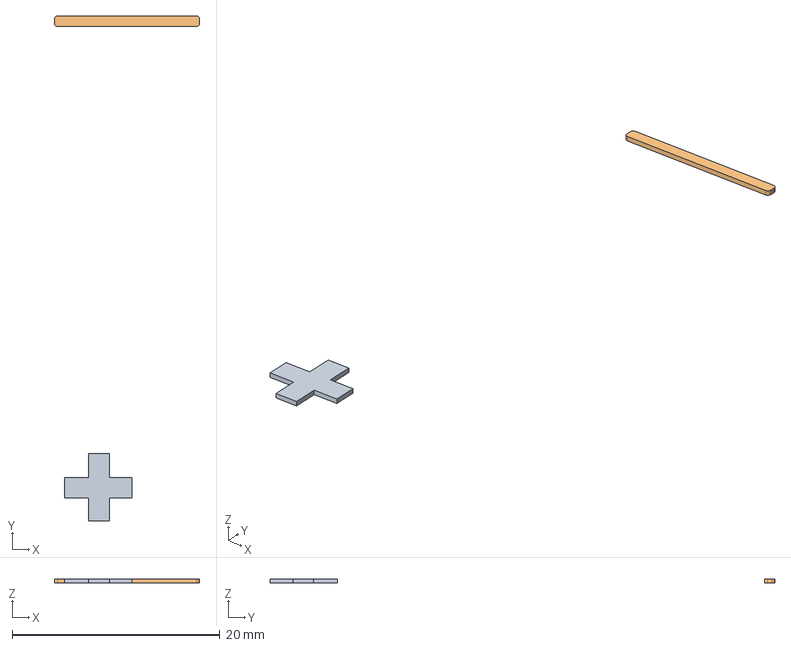
[picture p129: CAD file, 2026-09-29]
mechanical/revI/left-frame-nes-secondary.step
14.0 x 48.6 x 0.4 mm
