eduarbo/flan36/mechanical/revI/right-frame-manga-secondary.step

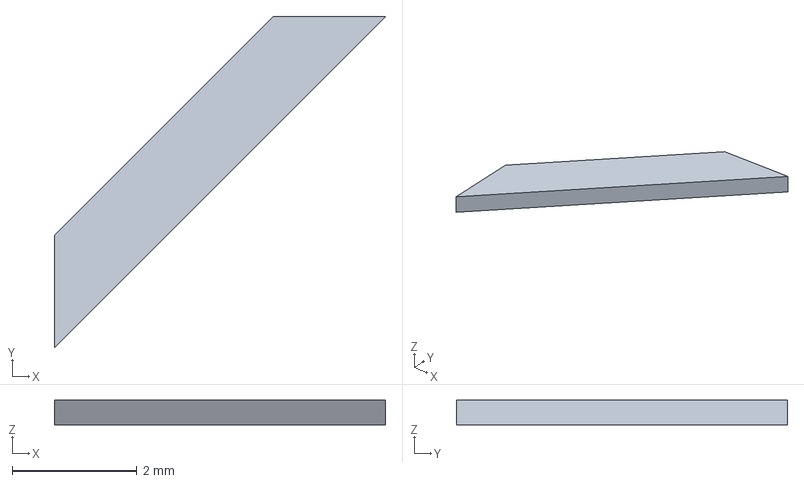
[picture p130: CAD file, 2026-09-29]
mechanical/revI/right-frame-manga-secondary.step
5.30 x 5.30 x 0.4 mm
