eduarbo/flan36/mechanical/revI/right-frame-flan-detail.step

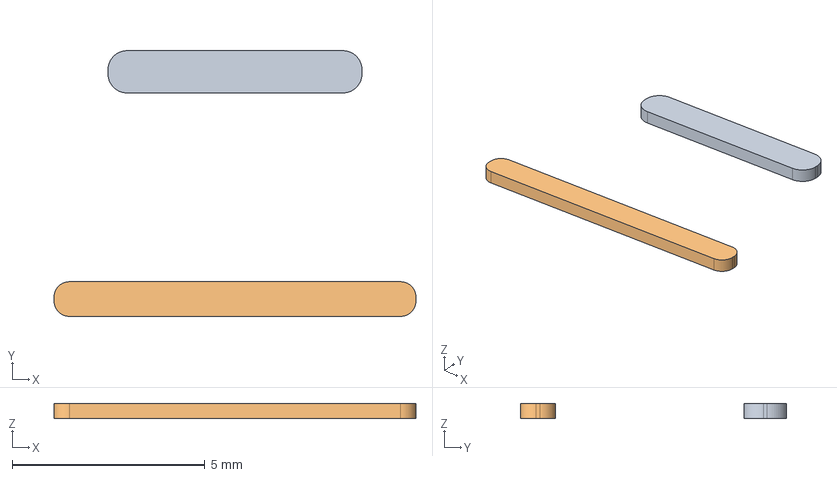
[picture p131: CAD file, 2026-09-29]
mechanical/revI/right-frame-flan-detail.step
9.40 x 6.90 x 0.4 mm
