eduarbo/flan36/mechanical/revI/left-frame-tape-accent.step

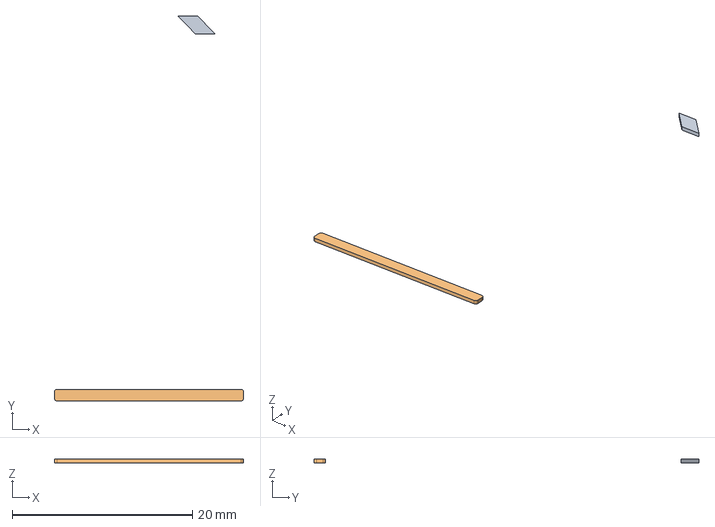
[picture p132: CAD file, 2026-09-29]
mechanical/revI/left-frame-tape-accent.step
21.0 x 42.7 x 0.4 mm
