eduarbo/flan36/mechanical/revI/left-frame-walkman-secondary.step

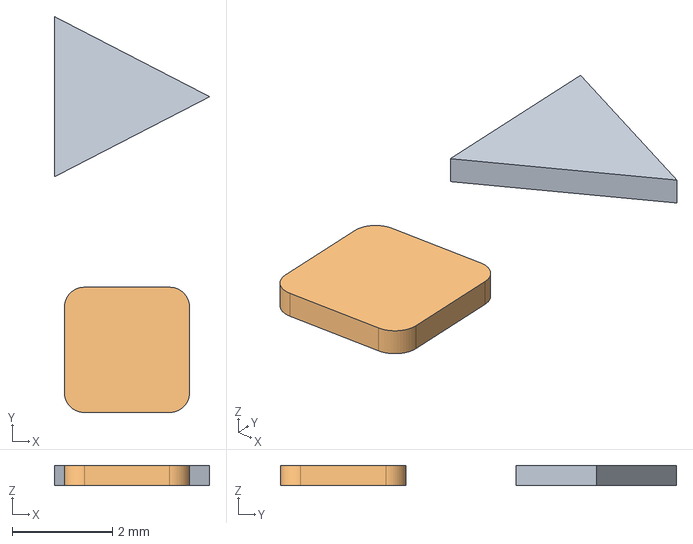
[picture p133: CAD file, 2026-09-29]
mechanical/revI/left-frame-walkman-secondary.step
3.10 x 7.90 x 0.4 mm
