eduarbo/flan36/mechanical/revI/left-frame-walkman-detail.step

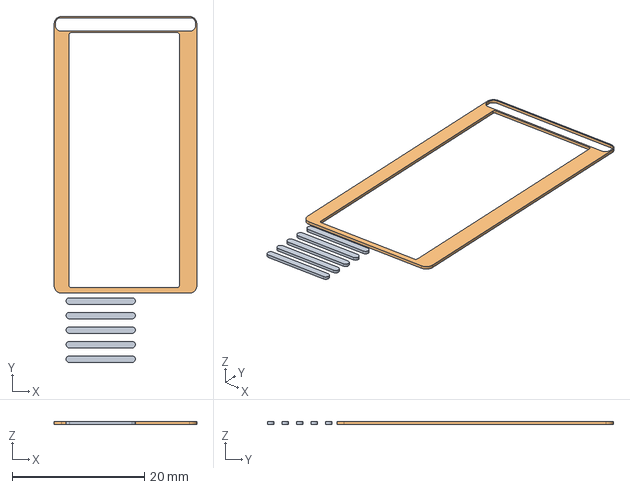
[picture p134: CAD file, 2026-09-29]
mechanical/revI/left-frame-walkman-detail.step
21.6 x 52.4 x 0.4 mm
