eduarbo/flan36/mechanical/revI/left-frame-nes-accent.step

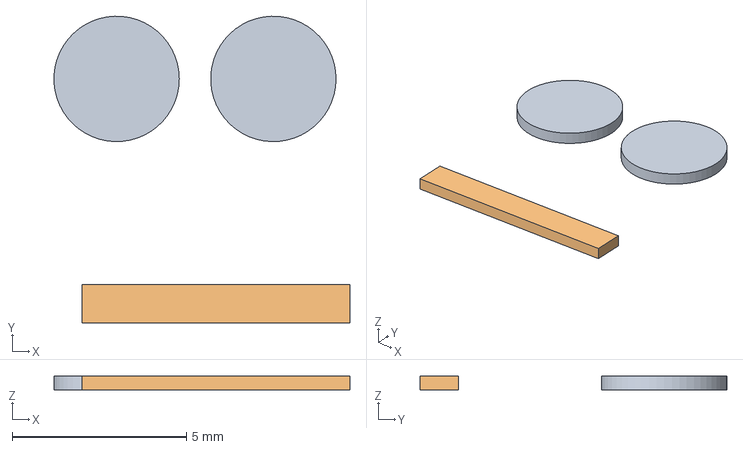
[picture p135: CAD file, 2026-09-29]
mechanical/revI/left-frame-nes-accent.step
8.50 x 8.80 x 0.4 mm
