eduarbo/flan36/mechanical/revI/left-frame-orbit-detail.step

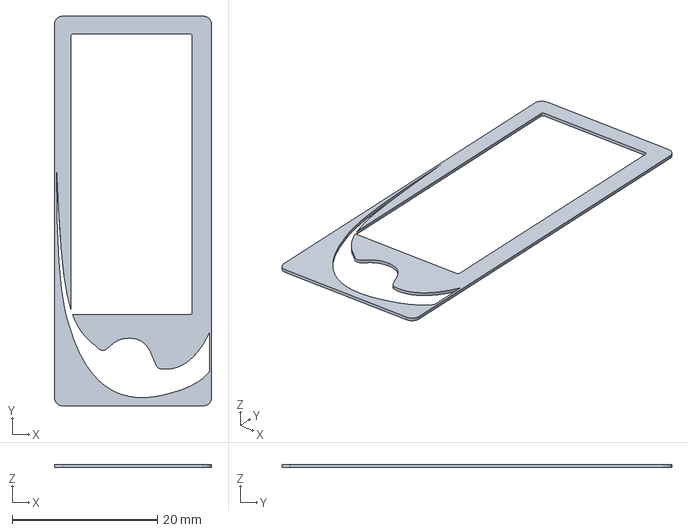
[picture p136: CAD file, 2026-09-29]
mechanical/revI/left-frame-orbit-detail.step
21.6 x 53.6 x 0.4 mm
