eduarbo/flan36/mechanical/revI/left-frame-orbit-secondary.step

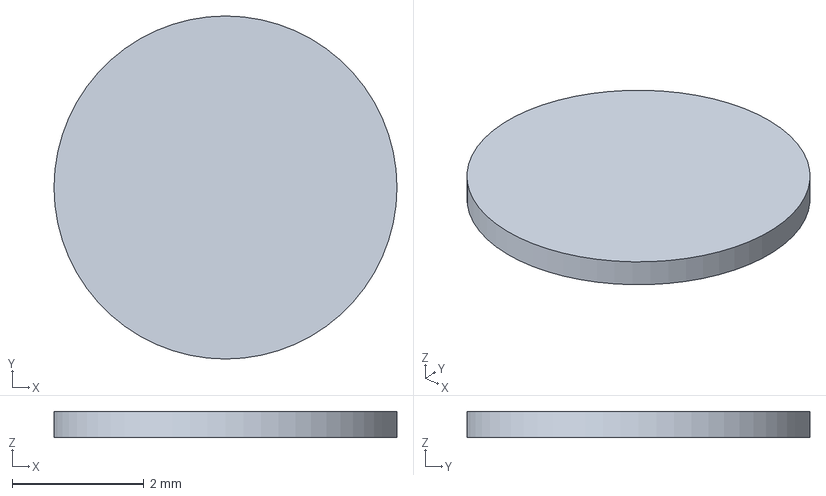
[picture p137: CAD file, 2026-09-29]
mechanical/revI/left-frame-orbit-secondary.step
5.20 x 5.20 x 0.4 mm
