eduarbo/flan36/mechanical/revI/right-frame-nes-detail.step

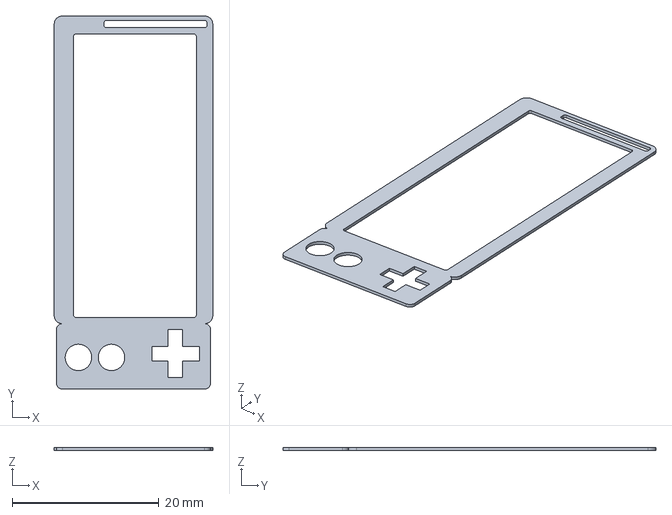
[picture p138: CAD file, 2026-09-29]
mechanical/revI/right-frame-nes-detail.step
21.6 x 50.8 x 0.4 mm
