eduarbo/flan36/mechanical/revI/left-frame-manga-detail.step

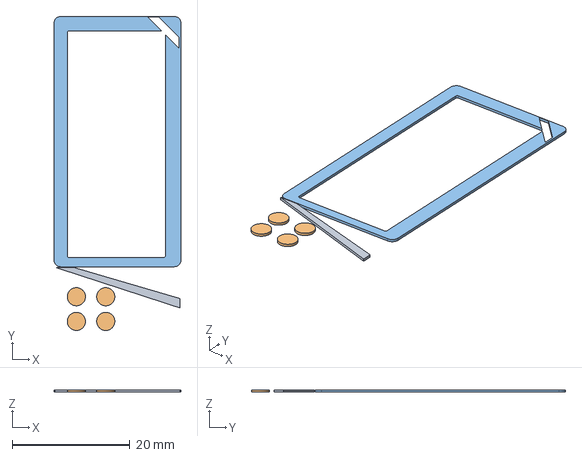
[picture p139: CAD file, 2026-09-29]
mechanical/revI/left-frame-manga-detail.step
21.6 x 53.4 x 0.4 mm
