eduarbo/flan36/mechanical/revI/right-frame-flan-secondary.step

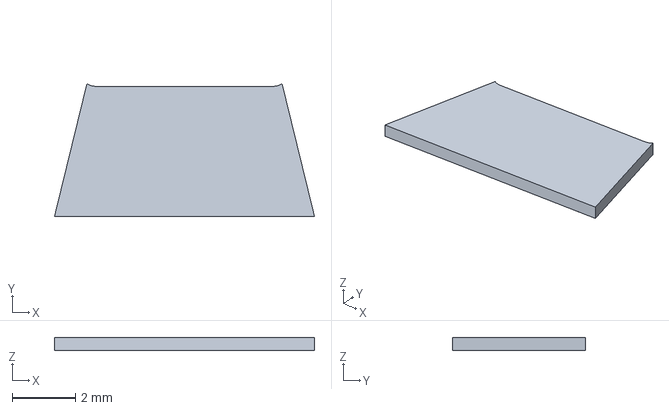
[picture p140: CAD file, 2026-09-29]
mechanical/revI/right-frame-flan-secondary.step
8.20 x 4.18 x 0.4 mm
