eduarbo/flan36/mechanical/revI/left-frame-walkman-accent.step

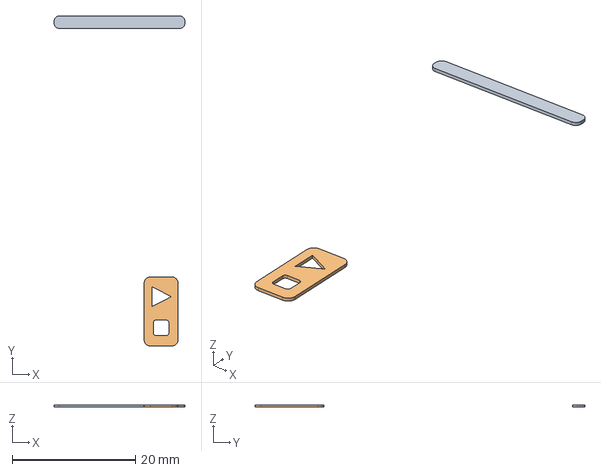
[picture p141: CAD file, 2026-09-29]
mechanical/revI/left-frame-walkman-accent.step
21.2 x 53.5 x 0.4 mm
