eduarbo/flan36/mechanical/revI/left-frame-tape-detail.step

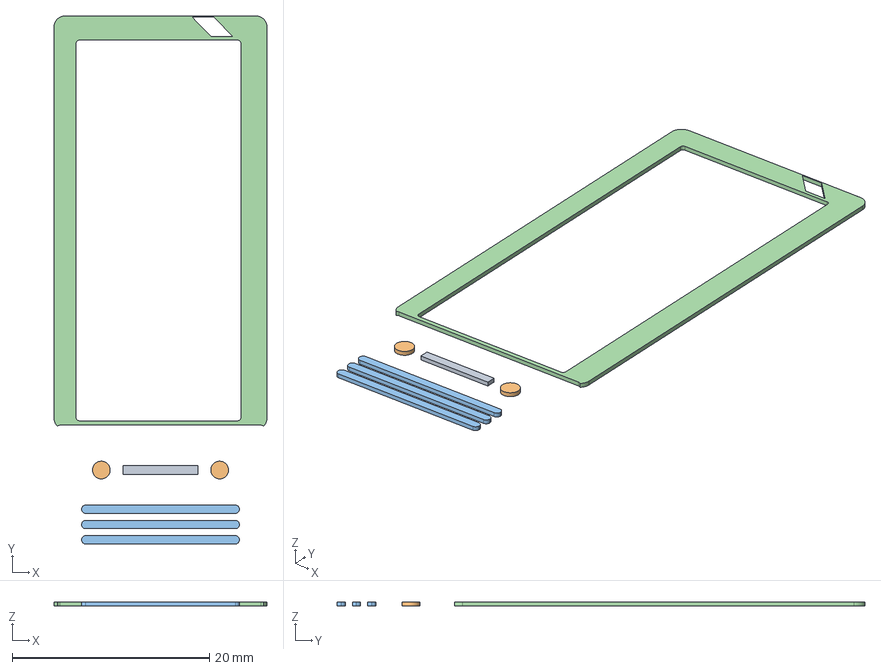
[picture p142: CAD file, 2026-09-29]
mechanical/revI/left-frame-tape-detail.step
21.6 x 53.5 x 0.4 mm
