eduarbo/flan36/mechanical/revI/right-frame-manga-accent.step

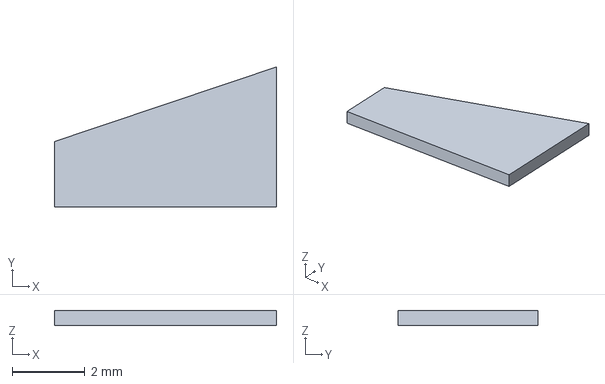
[picture p143: CAD file, 2026-09-29]
mechanical/revI/right-frame-manga-accent.step
6.10 x 3.85 x 0.4 mm
