eduarbo/flan36/tools/export_fabrication.py

#!/usr/bin/env python3
"""Export source-bound revI prototype Gerbers/drills after routed-board checks.
SPDX-License-Identifier: GPL-3.0-or-later
"""
import argparse
import hashlib
import json
from pathlib import Path
import shutil
import subprocess
import zipfile

ROOT = Path(__file__).resolve().parents[1]


def sha(path):
    return hashlib.sha256(path.read_bytes()).hexdigest()


def export(cli):
    receipt = json.loads((ROOT / 'validation/revI-routing.json').read_text())
    out = ROOT / 'hardware/revI/fabrication'; out.mkdir(exist_ok=True)
    result = {'schema': 'flan36-fabrication-1', 'physical_acceptance': False,
              'kicad_version': subprocess.check_output([cli, 'version'], text=True).strip(), 'halves': {}}
    for side, checks in receipt['halves'].items():
        stem = 'flan36-' + side
        pcb = ROOT / 'hardware/revI' / (stem + '.kicad_pcb')
        for suffix, key in (('.kicad_pcb','pcb_sha256'),('.kicad_sch','schematic_sha256'),('.kicad_pro','rules_sha256')):
            assert sha(pcb.with_suffix(suffix)) == checks[key], (side, 'Stale routing evidence')
        assert all(checks[k] == 0 for k in ('drc_violations','unconnected_items','schematic_parity','erc_violations'))
        directory = ROOT / 'build/fabrication' / side
        if directory.exists(): shutil.rmtree(directory)  # only this task's regenerable export
        directory.mkdir(parents=True)
        subprocess.run([cli,'pcb','export','gerbers','-l','F.Cu,B.Cu,F.Mask,B.Mask,F.Silkscreen,B.Silkscreen,Edge.Cuts',
                        '--subtract-soldermask','-o',str(directory)+'/',str(pcb)], check=True)
        subprocess.run([cli,'pcb','export','drill','--format','excellon','--excellon-units','mm',
                        '--excellon-separate-th','--generate-map','--map-format','svg',
                        '-o',str(directory)+'/',str(pcb)], check=True)
        expected = {'gtl','gbl','gts','gbs','gto','gbo','gm1'}
        assert expected <= {p.suffix[1:] for p in directory.iterdir()}
        assert (directory / (stem+'-PTH.drl')).is_file()
        assert (directory / (stem+'-NPTH.drl')).is_file()
        files = {p.name: sha(p) for p in sorted(directory.iterdir()) if p.is_file()}
        manifest = {'side':side,'source':checks,'files':files,'physical_acceptance':False,
                    'specification':{'copper_layers':2,'board_mm':1.6,'copper_oz':1,
                        'minimum_track_mm':.2,'netclass_clearance_mm':.2,'copper_edge_mm':.5},
                    'status':'Prototype candidate; confirm connectors, battery and assembly fit before ordering.'}
        (directory/'manifest.json').write_text(json.dumps(manifest,indent=2)+'\n')
        (directory/'README.txt').write_text('FLAN36 revI prototype candidate — '+side+'\n'
            'Two copper layers, 1.6 mm FR4, nominal 1 oz copper. Internal routed cutouts on Edge.Cuts.\n'
            'No panelization or assembly service is specified. Inspect Gerber and drill previews.\n'
            'Digital DRC/ERC/netlist checks passed. This is not a physically qualified build kit.\n'
            'Check exact connectors, cell dimensions/polarity, printed fit and retention before ordering.\n'
            'Build, BOM and hardware acceptance: https://github.com/eduarbo/flan36/blob/main/docs/build.md\n')
        package = out / (stem+'-revI-prototype.zip')
        with zipfile.ZipFile(package,'w',zipfile.ZIP_DEFLATED) as z:
            for file in sorted(directory.iterdir()): z.write(file,file.name)
        with zipfile.ZipFile(package) as z:
            assert z.testzip() is None
            for file, digest in files.items(): assert hashlib.sha256(z.read(file)).hexdigest() == digest
        result['halves'][side] = {'package':str(package.relative_to(ROOT)), 'sha256':sha(package), 'manifest':manifest}
    (ROOT/'validation/revI-fabrication.json').write_text(json.dumps(result,indent=2)+'\n')
    print('PASS: two source-bound prototype fabrication packages, ZIP readback verified')


if __name__ == '__main__':
    ap=argparse.ArgumentParser(description=__doc__)
    ap.add_argument('--cli',default='/Applications/KiCad/KiCad.app/Contents/MacOS/kicad-cli')
    export(ap.parse_args().cli)
