eduarbo/flan36/tools/check_viewer_revI.py

#!/usr/bin/env python3
"""Read-only provenance, key-layout and exact mesh-vertex check for the 3D viewer.
SPDX-License-Identifier: GPL-3.0-or-later
"""
import gzip
import base64
import hashlib
import json
import re
from pathlib import Path
import numpy as np
import vtk
from vtk.util.numpy_support import vtk_to_numpy

ROOT=Path(__file__).resolve().parents[1]
html=(ROOT/'docs/index.html').read_bytes()
receipt=json.loads((ROOT/'validation/revI-viewer.json').read_text())
assert hashlib.sha256(html).hexdigest()==receipt['viewer_sha256']
for source in receipt['sources']:
    assert hashlib.sha256((ROOT/source['path']).read_bytes()).hexdigest()==source['sha256'],source['path']
data=json.loads(gzip.decompress(base64.b64decode(re.search(rb'<script id="scene-data" type="application/octet-stream">(.*?)</script>',html,re.S)[1])))
model=json.loads((ROOT/'design/revI.json').read_text())
# Packed aliases retain the exact same geometry; inspect their original IDs too.
for alias,source in data.get('geometryAliases',{}).items():data['geometries'][alias]=data['geometries'][source]
catalog=data['catalog'];config=catalog['default_configuration'];variants={v['id']:v for v in catalog['variants']}
native_ids=[p['part_id'] for p in data['parts'] if 'part_id' in p]
assert len(native_ids)==len(set(native_ids)) and set(native_ids)==set(model['parts']), 'Every exported assembly part must appear exactly once in the viewer'
assert len(data['parts'])==len(model['parts'])+36*3+8+2, 'Native assembly plus 36 keys, 72 switch objects, 8 feet and 2 screens'
for side in ('left','right'):
    sockets=[p for p in data['parts'] if p.get('part_id')==side+'-display-socket']
    assert len(sockets)==1 and sockets[0]['group']=='connectors', 'Retained J2 must be explicit in each half'
for side in ('left','right'):
    bounds=data['geometries'][f'mechanical/revI/{side}-battery.stl']['bounds_mm']
    native=model['parts'][side+'-battery']['bounds_mm']
    expected=[[native[0],native[2],-native[4]],[native[3],native[5],-native[1]]]
    assert np.allclose(bounds,expected,rtol=0,atol=1e-4),(side,'unplaced battery')
    assert abs(bounds[0][1]-model['parameter_values_mm']['BatteryBottom'])<1e-5,(side,'battery datum')
layout=json.loads((ROOT/'design/layout.json').read_text())
caps=[p for p in data['parts'] if p['group']=='keycaps'];assert len(caps)==36
for side,keys in layout['halves'].items():
    for k in keys:
        p=next(p for p in caps if p['name']==side+' · KLP '+k['ref'])
        choice=config['keycaps'][side][k['ref']];variant=variants[choice['variant']]
        assert p['position']==[(161 if side=='right' else 0)+k['x'],variant['seating_z_mm'],k['y']]
        assert p['angle_deg']==k['angle']+choice['rotation_deg']
for ident,leads in model['batteryLeadProfiles'].items():
    assert data['batteryLeadProfiles'][ident]==[{'index':wire['index'],'geometry':'mechanical/revI/'+wire['stl'],
        'color':wire.get('color','#ad453d' if wire['index']==0 else '#353738')} for wire in leads],ident
switches=json.loads((ROOT/'components/switches.json').read_text())
decode=lambda g,k,dtype:np.frombuffer(base64.b64decode(g[k]),dtype=dtype)
for path,g in data['geometries'].items():
    if g.get('material_parts'):
        ident=Path(path).stem.replace('-frame-','-',1)
        native=model['frameVariants'][ident]['material_parts']
        assert g['material_parts']==[{'role':p['role'],'path':'mechanical/revI/'+p['stl']} for p in native]
        roles=['body','detail','accent','secondary'];ps=[];ns=[];ix=[];vertex=0;offset=0
        for i,part in enumerate(g['material_parts']):
            child=data['geometries'][part['path']]
            p=decode(child,'positions','<f4');n=decode(child,'normals','<f4');indices=decode(child,'indices','<u4')
            ps.append(p);ns.append(n);ix.append(indices+vertex)
            assert g['groups'][i]=={'start':offset,'count':len(indices),'materialIndex':roles.index(part['role'])}
            vertex+=len(p)//3;offset+=len(indices)
        assert np.array_equal(decode(g,'positions','<f4'),np.concatenate(ps)),path
        assert np.array_equal(decode(g,'normals','<f4'),np.concatenate(ns)),path
        assert np.array_equal(decode(g,'indices','<u4'),np.concatenate(ix)),path
        assert offset==g['triangles']*3
        continue
    if path.endswith('#materials'):
        part=next(p for p in data['parts'] if p.get('geometry')==path)
        parent=path.removesuffix('#materials')
        visuals=switches[parent] if parent in switches else model['parts'][Path(parent).stem]['visuals']
        assert part['materials']==[v['color'] for v in visuals]
        assert len(part['materials'])==len(g['groups'])
        ps=[];ns=[];ix=[];vertex=0;offset=0
        for i,v in enumerate(visuals):
            child=data['geometries'][v['path']];p=decode(child,'positions','<f4');n=decode(child,'normals','<f4');indices=decode(child,'indices','<u4')
            ps.append(p);ns.append(n);ix.append(indices+vertex)
            assert g['groups'][i]=={'start':offset,'count':len(indices),'materialIndex':i}
            vertex+=len(p)//3;offset+=len(indices)
        assert np.array_equal(decode(g,'positions','<f4'),np.concatenate(ps)),path
        assert np.array_equal(decode(g,'normals','<f4'),np.concatenate(ns)),path
        assert np.array_equal(decode(g,'indices','<u4'),np.concatenate(ix)),path
        assert offset==g['triangles']*3
        continue
    reader=vtk.vtkSTLReader();reader.SetFileName(str(ROOT/path));reader.Update();mesh=reader.GetOutput()
    expected=vtk_to_numpy(mesh.GetPoints().GetData()).copy()[:,[0,2,1]]
    if path.startswith('mechanical/revI/'):expected[:,2]*=-1
    actual=np.frombuffer(base64.b64decode(g['positions']),dtype='<f4').reshape(-1,3)
    assert set(map(tuple,actual))==set(map(tuple,expected)),path
    assert g['triangles']==mesh.GetNumberOfCells(),path
print(f'PASS: viewer and sources match; 36 key positions/angles; {len(data["geometries"])} meshes preserve vertices and triangle counts.')
